Lee-Txwg/Miner_Helmet/06_FCT/Wordpress/wp-content/themes/twentytwentyfour/assets/images/tourist-and-building.webp

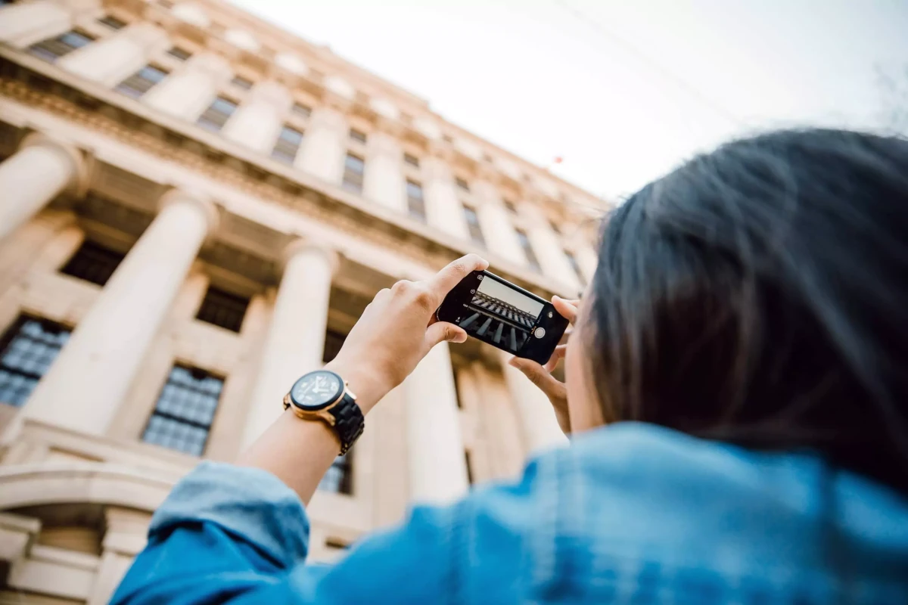
06_FCT/Wordpress/wp-content/themes/twentytwentyfour/assets/images/tourist-and-building.webp
