Lee-Txwg/Miner_Helmet/04_Software/00_Ref/【挽救小白第一季】STM32+8266+小程序智能家居毕设实战/1.使用模块硬件资料/3.esp01s网络模块/接线示例.png

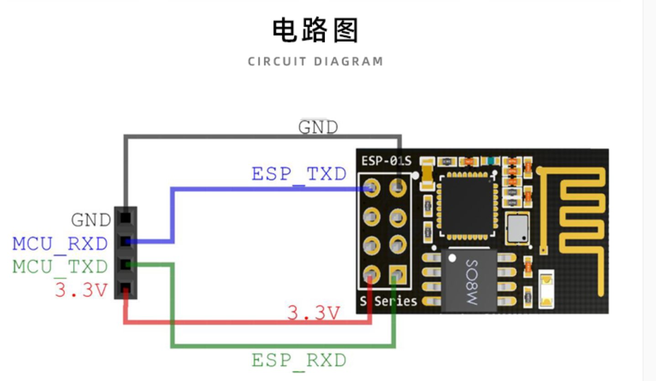
04_Software/00_Ref/【挽救小白第一季】STM32+8266+小程序智能家居毕设实战/1.使用模块硬件资料/3.esp01s网络模块/接线示例.png
