Lee-Txwg/Miner_Helmet/04_Software/00_Ref/【挽救小白第一季】STM32+8266+小程序智能家居毕设实战/1.使用模块硬件资料/4.STM32F103C8T6核心板/尺寸.jpg

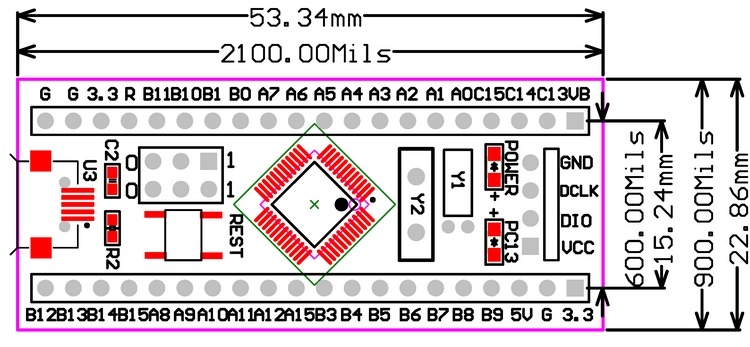
04_Software/00_Ref/【挽救小白第一季】STM32+8266+小程序智能家居毕设实战/1.使用模块硬件资料/4.STM32F103C8T6核心板/尺寸.jpg
