Lee-Txwg/Miner_Helmet/04_Software/00_Ref/【挽救小白第一季】STM32+8266+小程序智能家居毕设实战/2.扩展板硬件设计资料/v1.5(在售)/1.预览图片/2D_bottom_v1.5.png

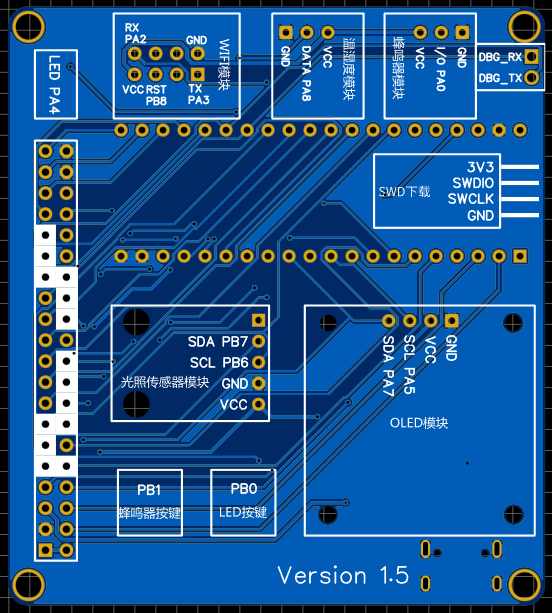
04_Software/00_Ref/【挽救小白第一季】STM32+8266+小程序智能家居毕设实战/2.扩展板硬件设计资料/v1.5(在售)/1.预览图片/2D_bottom_v1.5.png
