Lee-Txwg/Miner_Helmet/06_FCT/Wordpress/wp-admin/images/about-texture.png

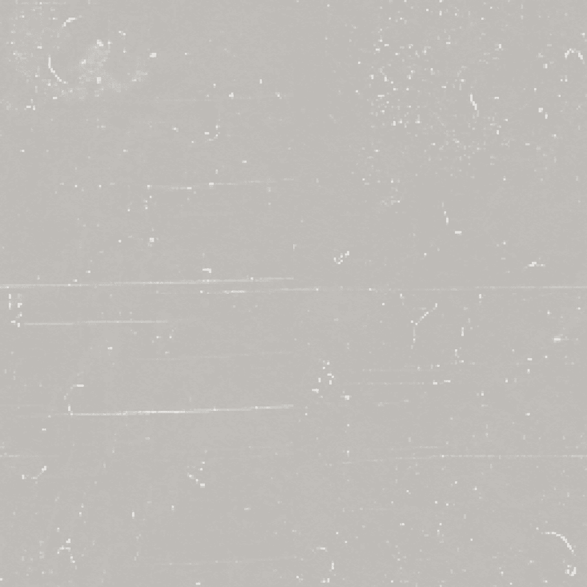
06_FCT/Wordpress/wp-admin/images/about-texture.png
