Lee-Txwg/Miner_Helmet/06_FCT/Wordpress/wp-admin/images/browser-rtl.png

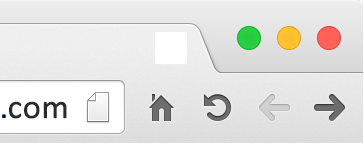
06_FCT/Wordpress/wp-admin/images/browser-rtl.png
