Lee-Txwg/Miner_Helmet/06_FCT/Wordpress/wp-admin/images/wheel.png

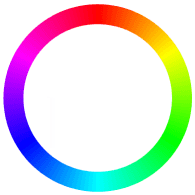
06_FCT/Wordpress/wp-admin/images/wheel.png
