Lee-Txwg/Miner_Helmet/06_FCT/Wordpress/wp-content/themes/twentytwentyfive/assets/images/404-image.webp

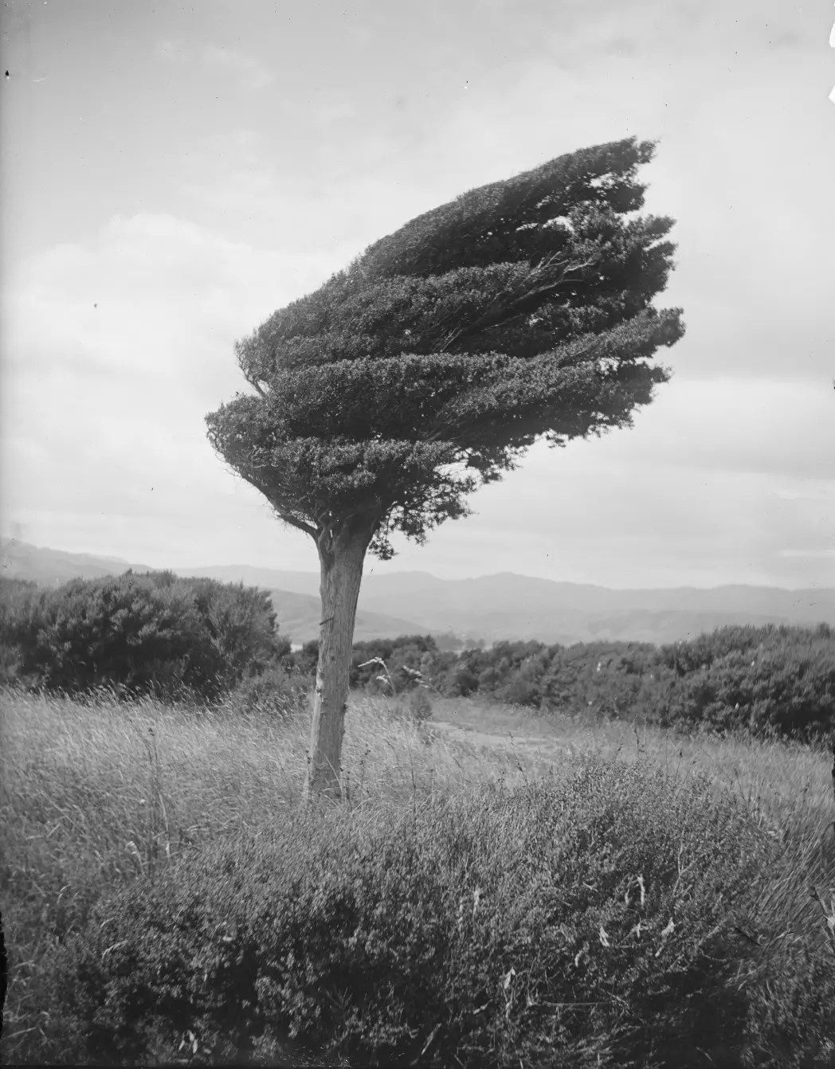
06_FCT/Wordpress/wp-content/themes/twentytwentyfive/assets/images/404-image.webp
