Lee-Txwg/Miner_Helmet/06_FCT/Wordpress/wp-content/themes/twentytwentyfive/assets/images/agenda-img-4.webp

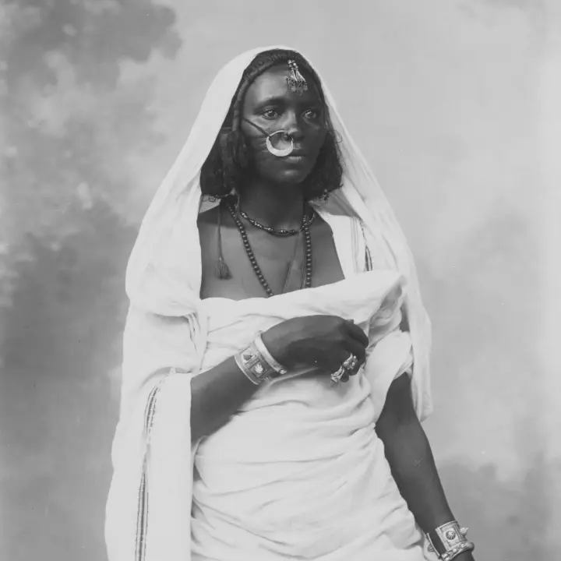
06_FCT/Wordpress/wp-content/themes/twentytwentyfive/assets/images/agenda-img-4.webp
