Lee-Txwg/Miner_Helmet/06_FCT/Wordpress/wp-content/themes/twentytwentyfive/assets/images/akaka-falls-state-park-flora.webp

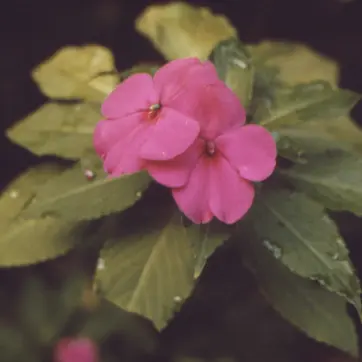
06_FCT/Wordpress/wp-content/themes/twentytwentyfive/assets/images/akaka-falls-state-park-flora.webp
