Lee-Txwg/Miner_Helmet/06_FCT/Wordpress/wp-content/themes/twentytwentyfive/assets/images/book-image-landing.webp

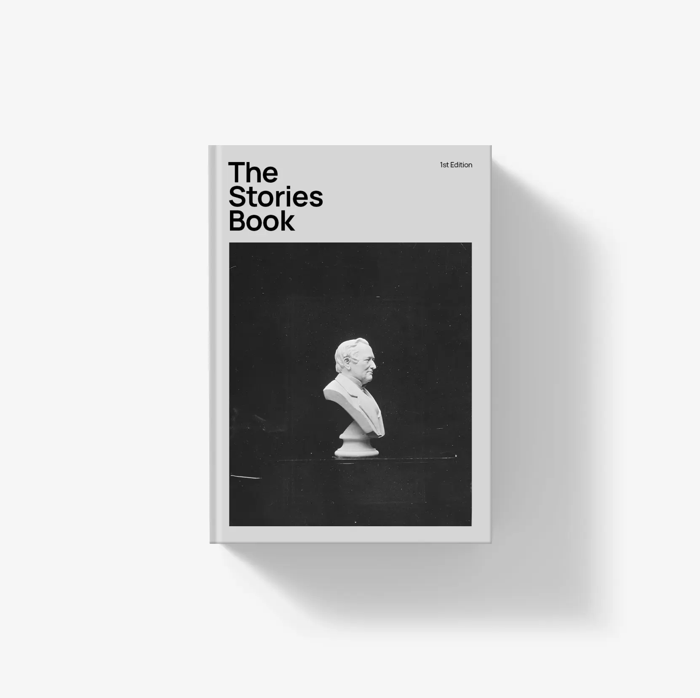
06_FCT/Wordpress/wp-content/themes/twentytwentyfive/assets/images/book-image-landing.webp
