Lee-Txwg/Miner_Helmet/06_FCT/Wordpress/wp-content/themes/twentytwentyfive/assets/images/flower-meadow-square.webp

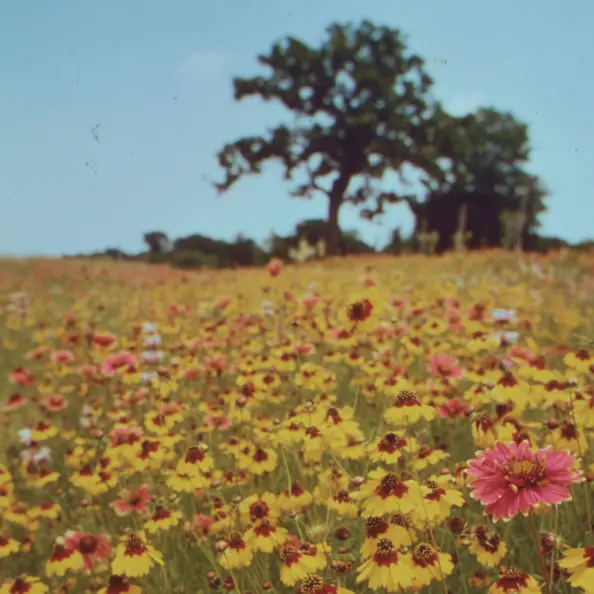
06_FCT/Wordpress/wp-content/themes/twentytwentyfive/assets/images/flower-meadow-square.webp
