Lee-Txwg/Miner_Helmet/06_FCT/Wordpress/wp-content/themes/twentytwentyfive/assets/images/grid-flower-1.webp

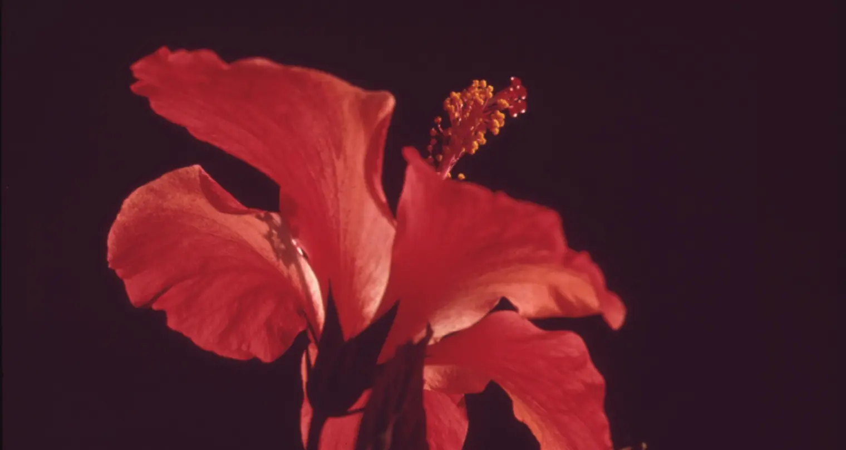
06_FCT/Wordpress/wp-content/themes/twentytwentyfive/assets/images/grid-flower-1.webp
