Lee-Txwg/Miner_Helmet/06_FCT/Wordpress/wp-content/themes/twentytwentyfive/assets/images/hero-podcast.webp

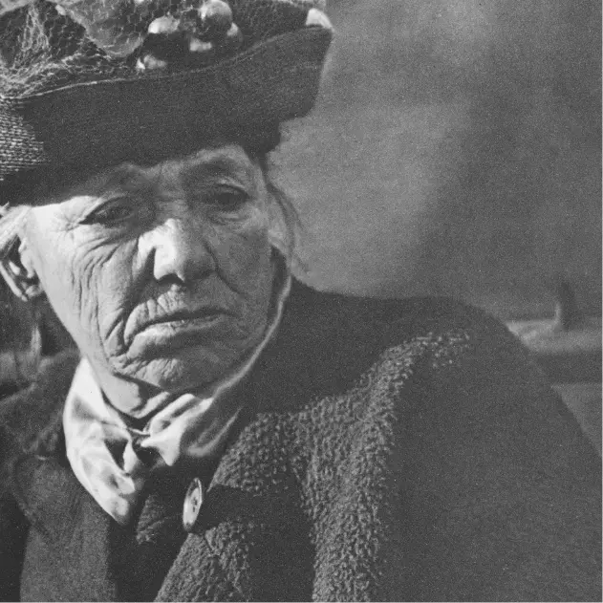
06_FCT/Wordpress/wp-content/themes/twentytwentyfive/assets/images/hero-podcast.webp
