Lee-Txwg/Miner_Helmet/06_FCT/Wordpress/wp-content/themes/twentytwentyfive/assets/images/link-in-bio-background.webp

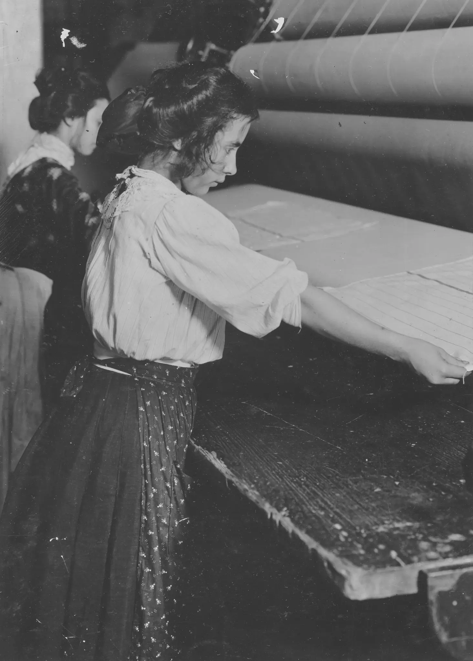
06_FCT/Wordpress/wp-content/themes/twentytwentyfive/assets/images/link-in-bio-background.webp
