Lee-Txwg/Miner_Helmet/06_FCT/Wordpress/wp-content/themes/twentytwentyfive/assets/images/man-in-hat.webp

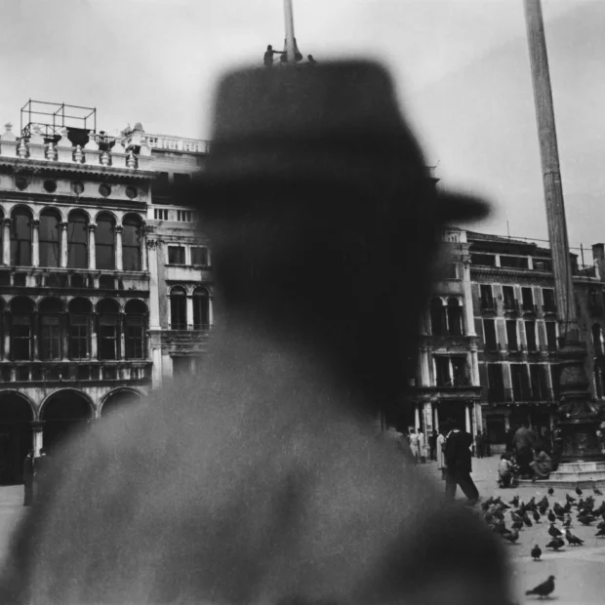
06_FCT/Wordpress/wp-content/themes/twentytwentyfive/assets/images/man-in-hat.webp
