Lee-Txwg/Miner_Helmet/06_FCT/Wordpress/wp-content/themes/twentytwentyfive/assets/images/northern-buttercups-flowers.webp

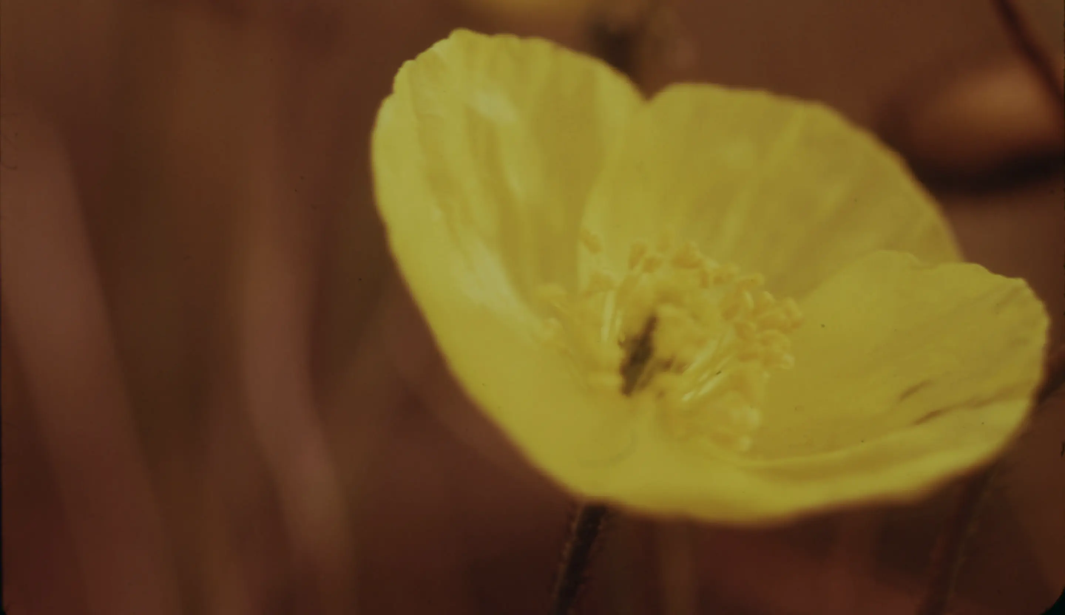
06_FCT/Wordpress/wp-content/themes/twentytwentyfive/assets/images/northern-buttercups-flowers.webp
