Lee-Txwg/Miner_Helmet/06_FCT/Wordpress/wp-content/themes/twentytwentyfive/assets/images/red-hibiscus-closeup.webp

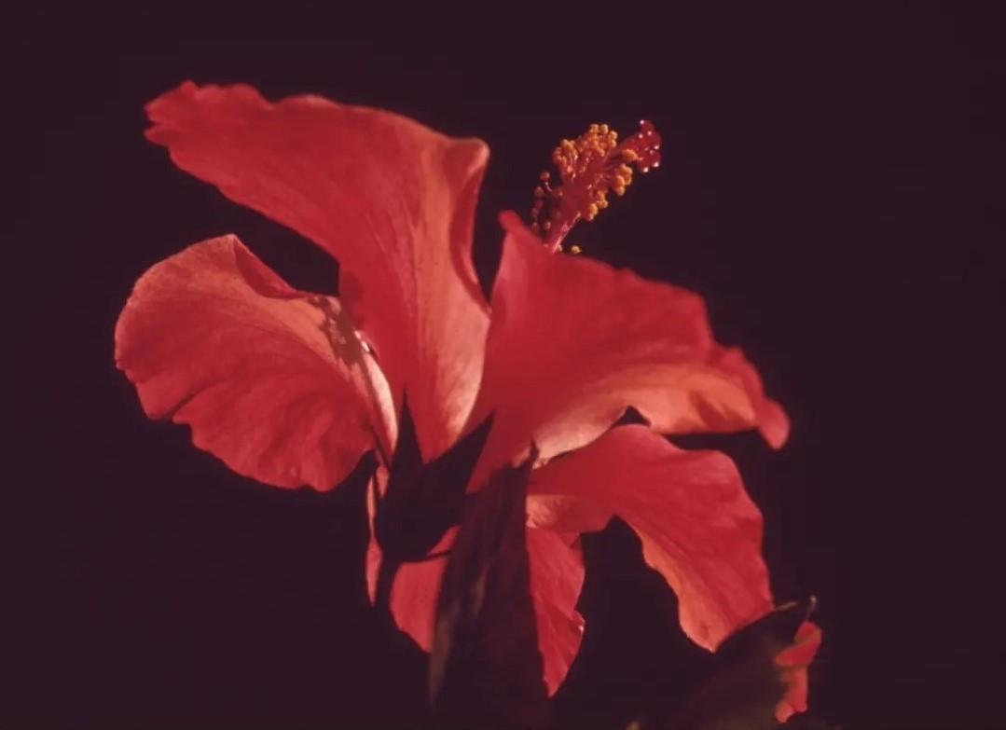
06_FCT/Wordpress/wp-content/themes/twentytwentyfive/assets/images/red-hibiscus-closeup.webp
