Lee-Txwg/Miner_Helmet/06_FCT/Wordpress/wp-content/themes/twentytwentyfive/assets/images/services-subscriber-photo.webp

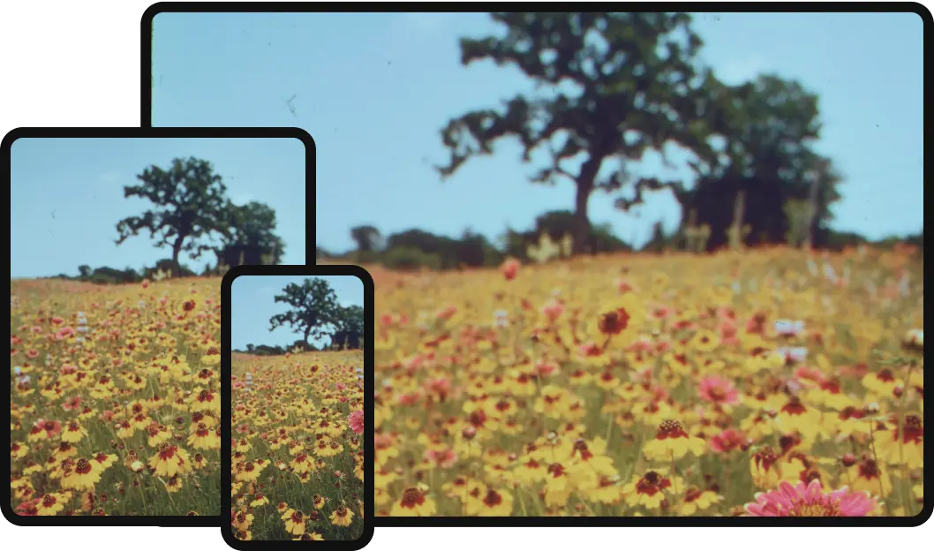
06_FCT/Wordpress/wp-content/themes/twentytwentyfive/assets/images/services-subscriber-photo.webp
