Lee-Txwg/Miner_Helmet/06_FCT/Wordpress/wp-content/themes/twentytwentyfive/assets/images/star-thristle-flower.webp

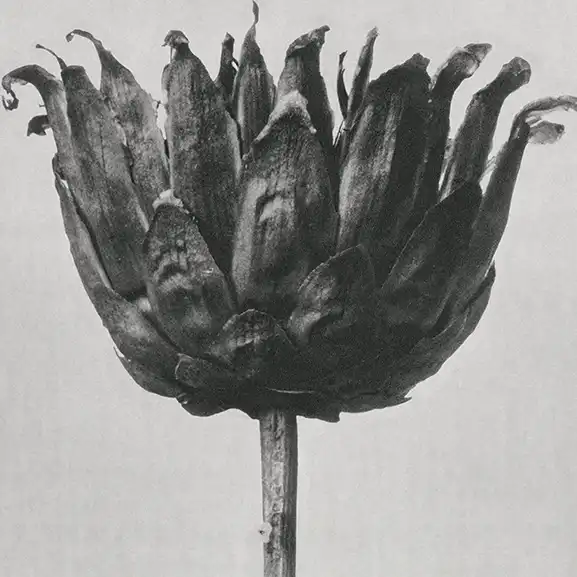
06_FCT/Wordpress/wp-content/themes/twentytwentyfive/assets/images/star-thristle-flower.webp
