Lee-Txwg/Miner_Helmet/06_FCT/Wordpress/wp-content/themes/twentytwentyfive/screenshot.png

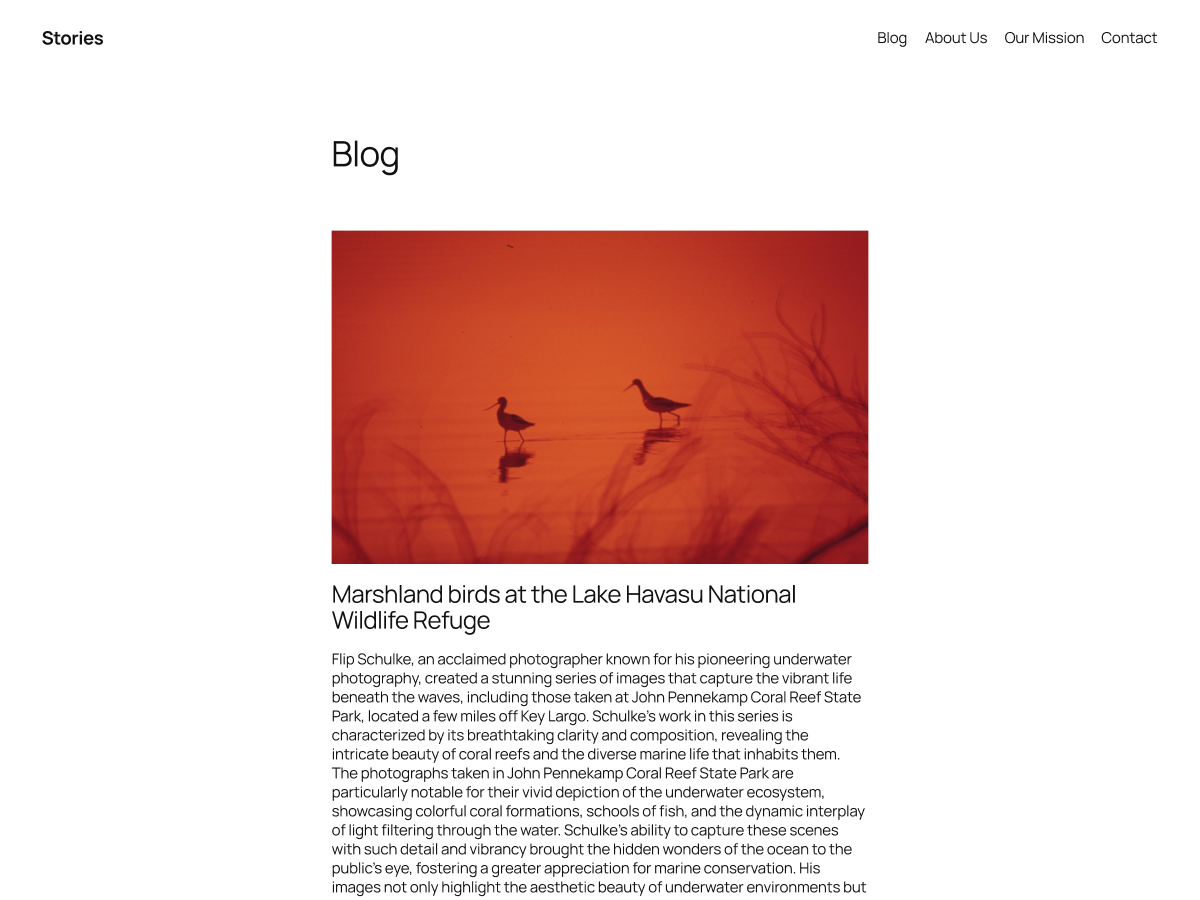
06_FCT/Wordpress/wp-content/themes/twentytwentyfive/screenshot.png
