Lee-Txwg/Miner_Helmet/06_FCT/Wordpress/wp-content/themes/twentytwentyfour/assets/images/abstract-geometric-art.webp

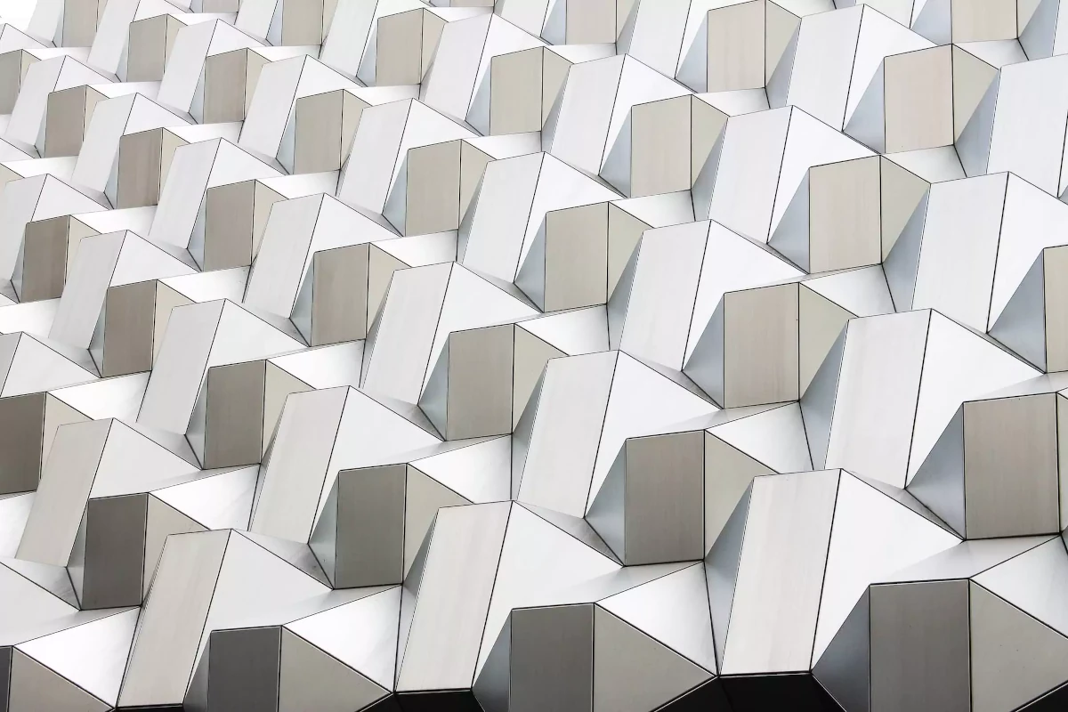
06_FCT/Wordpress/wp-content/themes/twentytwentyfour/assets/images/abstract-geometric-art.webp
