Lee-Txwg/Miner_Helmet/06_FCT/Wordpress/wp-content/themes/twentytwentyfour/assets/images/green-staircase.webp

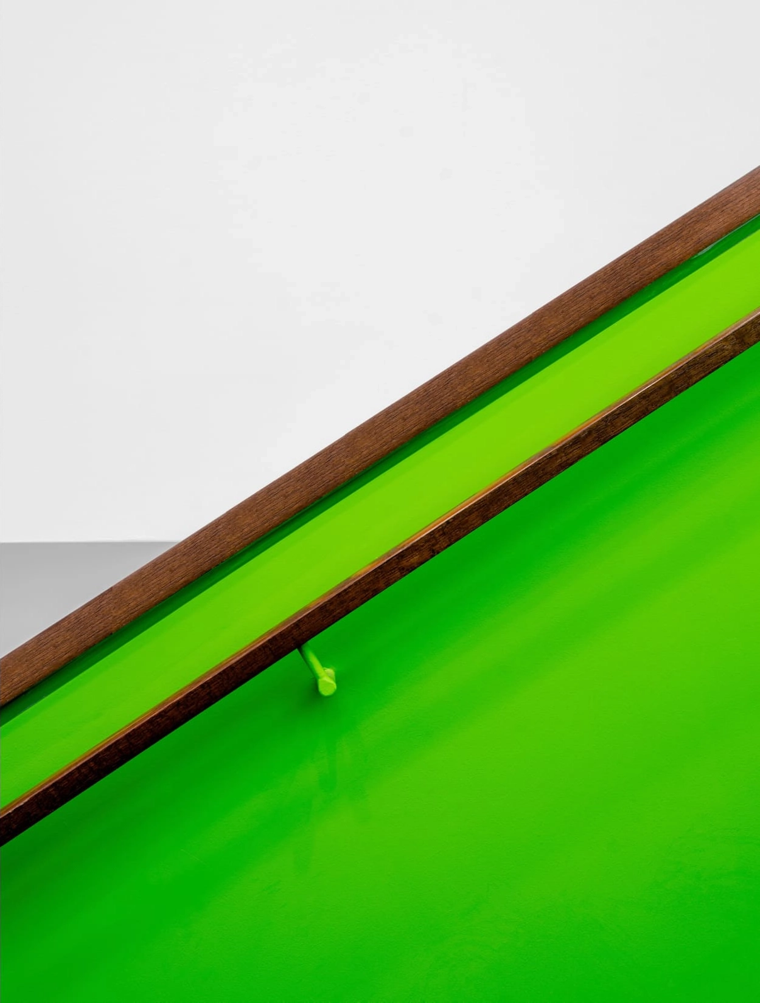
06_FCT/Wordpress/wp-content/themes/twentytwentyfour/assets/images/green-staircase.webp
