Lee-Txwg/Miner_Helmet/06_FCT/Wordpress/wp-content/themes/twentytwentyfour/assets/images/hotel-facade.webp

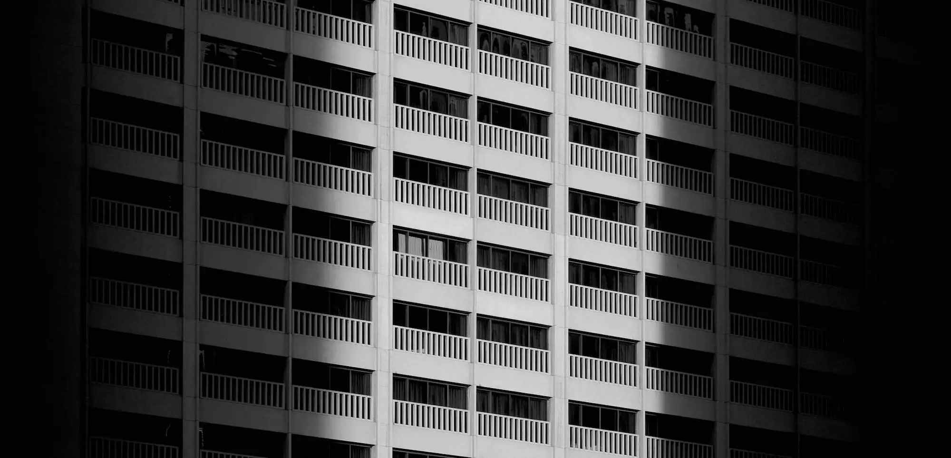
06_FCT/Wordpress/wp-content/themes/twentytwentyfour/assets/images/hotel-facade.webp
