Lee-Txwg/Miner_Helmet/06_FCT/Wordpress/wp-content/themes/twentytwentyfour/assets/images/museum.webp

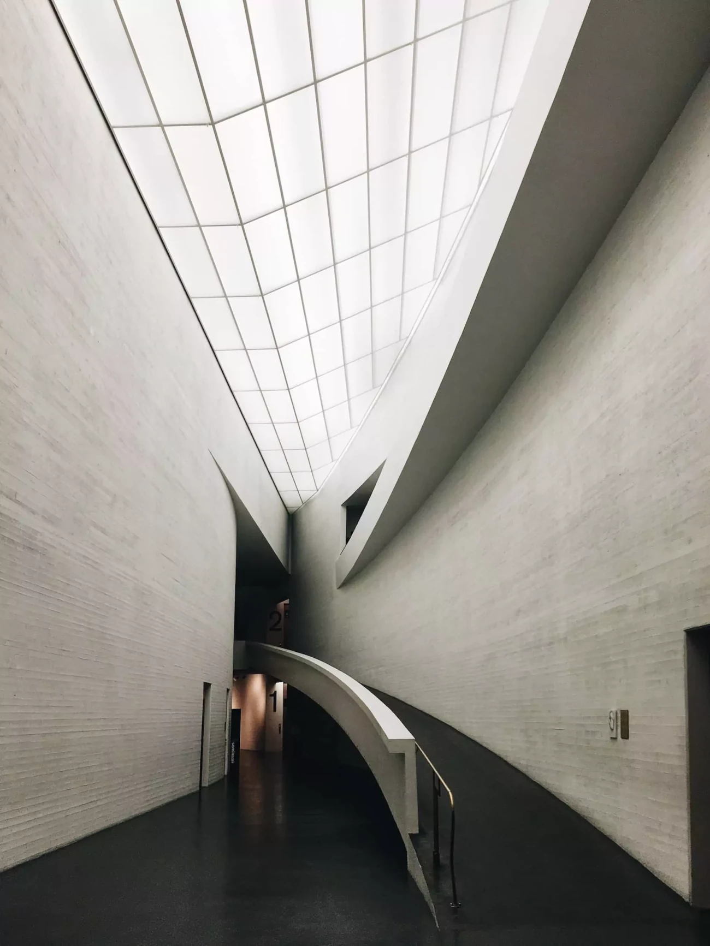
06_FCT/Wordpress/wp-content/themes/twentytwentyfour/assets/images/museum.webp
