Lee-Txwg/Miner_Helmet/06_FCT/Wordpress/wp-content/themes/twentytwentythree/screenshot.png

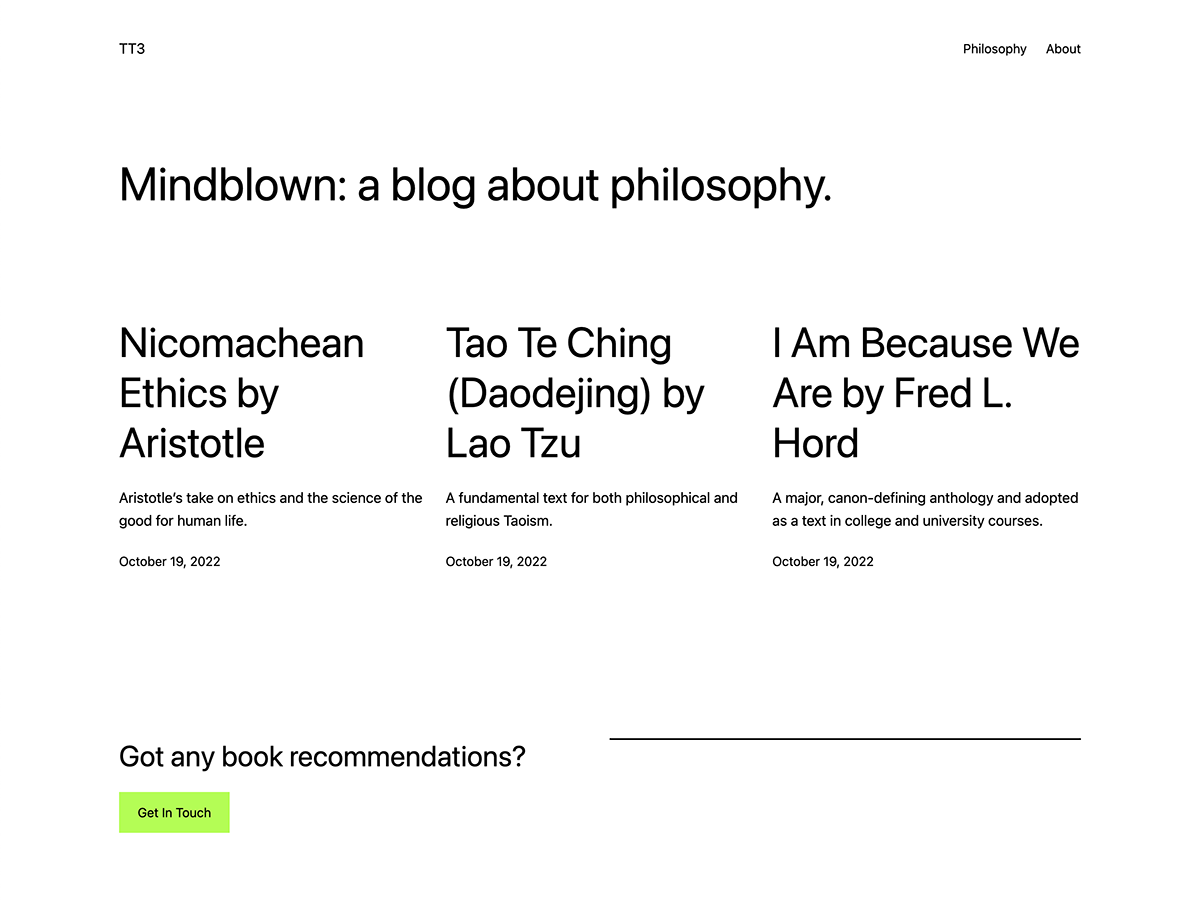
06_FCT/Wordpress/wp-content/themes/twentytwentythree/screenshot.png
