Lee-Txwg/Miner_Helmet/06_FCT/Wordpress/wp-content/themes/twentytwentytwo/assets/images/bird-on-black.jpg

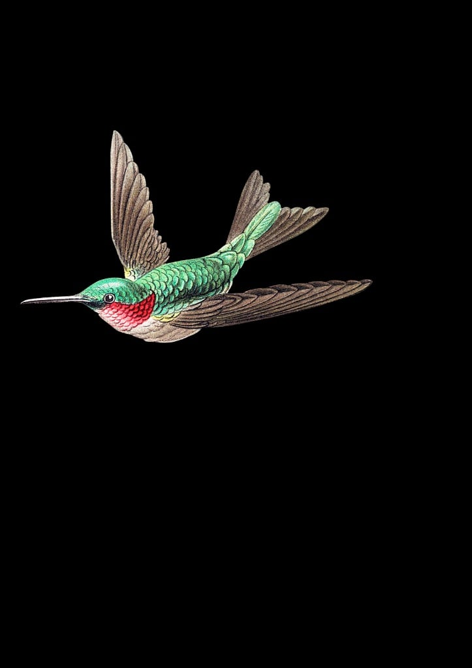
06_FCT/Wordpress/wp-content/themes/twentytwentytwo/assets/images/bird-on-black.jpg
