Lee-Txwg/Miner_Helmet/06_FCT/Wordpress/wp-content/themes/twentytwentytwo/assets/images/divider-black.png

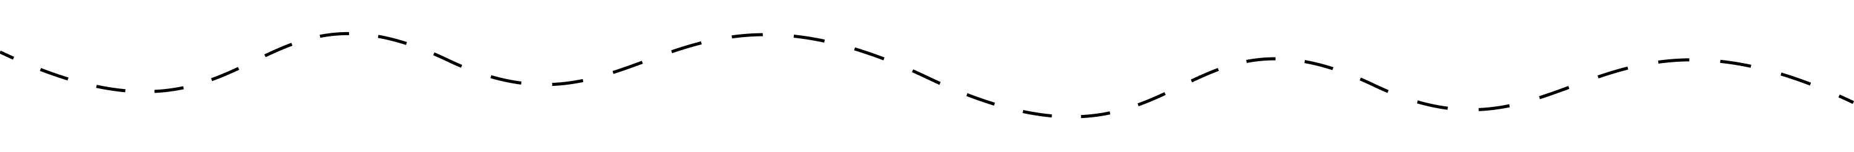
06_FCT/Wordpress/wp-content/themes/twentytwentytwo/assets/images/divider-black.png
