Lee-Txwg/Miner_Helmet/06_FCT/Wordpress/wp-content/themes/twentytwentytwo/assets/images/divider-white.png

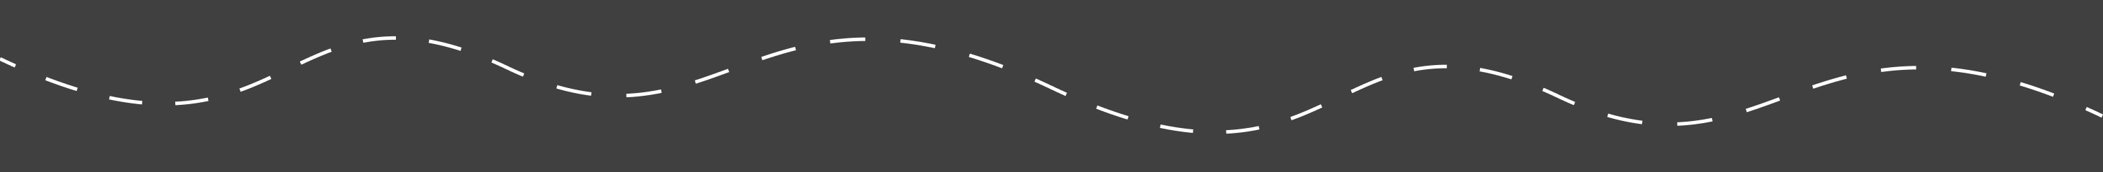
06_FCT/Wordpress/wp-content/themes/twentytwentytwo/assets/images/divider-white.png
