Lee-Txwg/Miner_Helmet/06_FCT/Wordpress/wp-content/themes/twentytwentytwo/assets/images/ducks.jpg

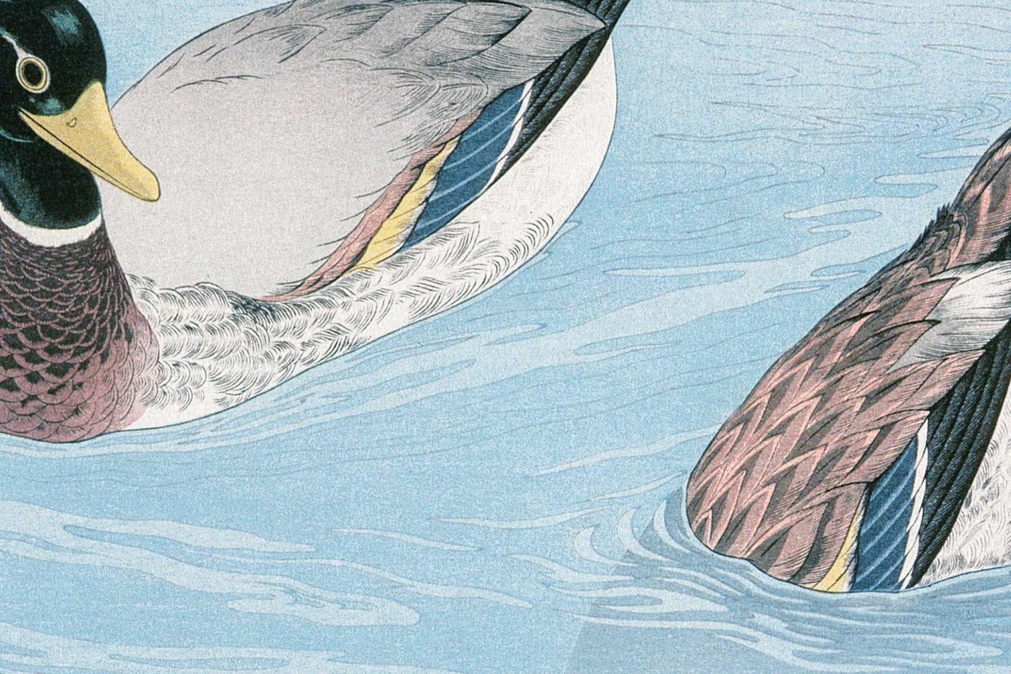
06_FCT/Wordpress/wp-content/themes/twentytwentytwo/assets/images/ducks.jpg
