Lee-Txwg/Miner_Helmet/06_FCT/Wordpress/wp-content/themes/twentytwentytwo/assets/images/flight-path-on-salmon.jpg

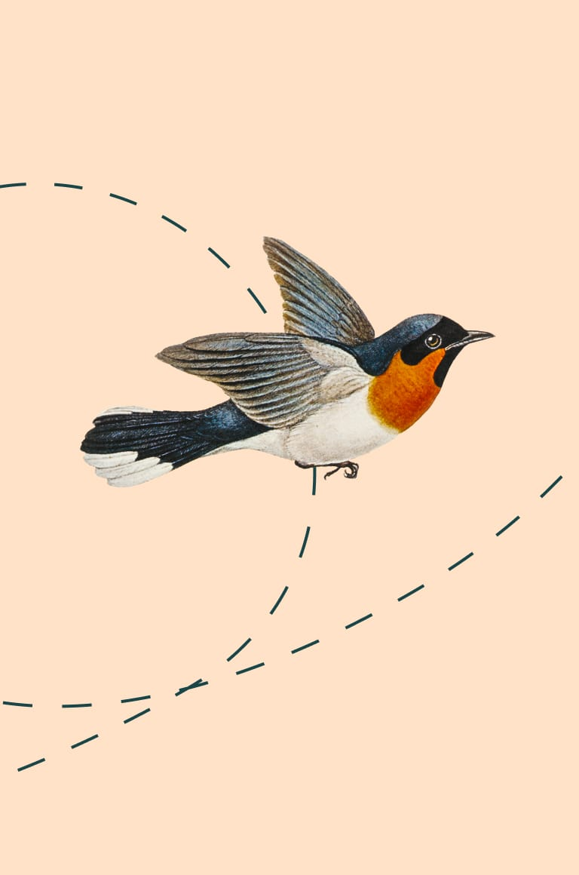
06_FCT/Wordpress/wp-content/themes/twentytwentytwo/assets/images/flight-path-on-salmon.jpg
