Lee-Txwg/Miner_Helmet/06_FCT/Wordpress/wp-content/themes/twentytwentytwo/screenshot.png

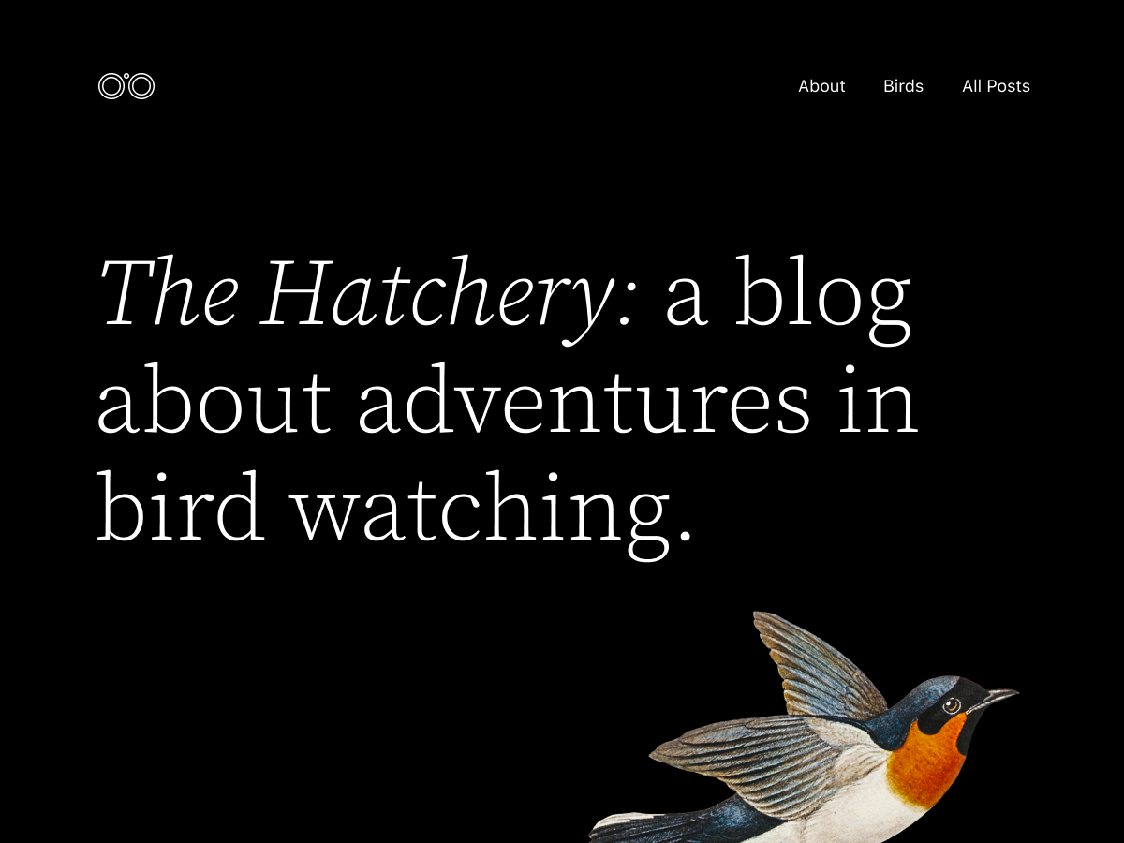
06_FCT/Wordpress/wp-content/themes/twentytwentytwo/screenshot.png
