Lee-Txwg/Miner_Helmet/06_FCT/Wordpress/wp-includes/js/mediaelement/mejs-controls.png

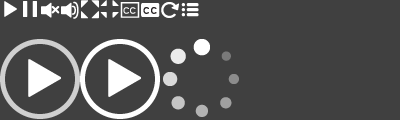
06_FCT/Wordpress/wp-includes/js/mediaelement/mejs-controls.png
