Lee-Txwg/Miner_Helmet/02_Hardware/01_Project/01_AD/MineSafe-circular-board/material/Doc1.docx

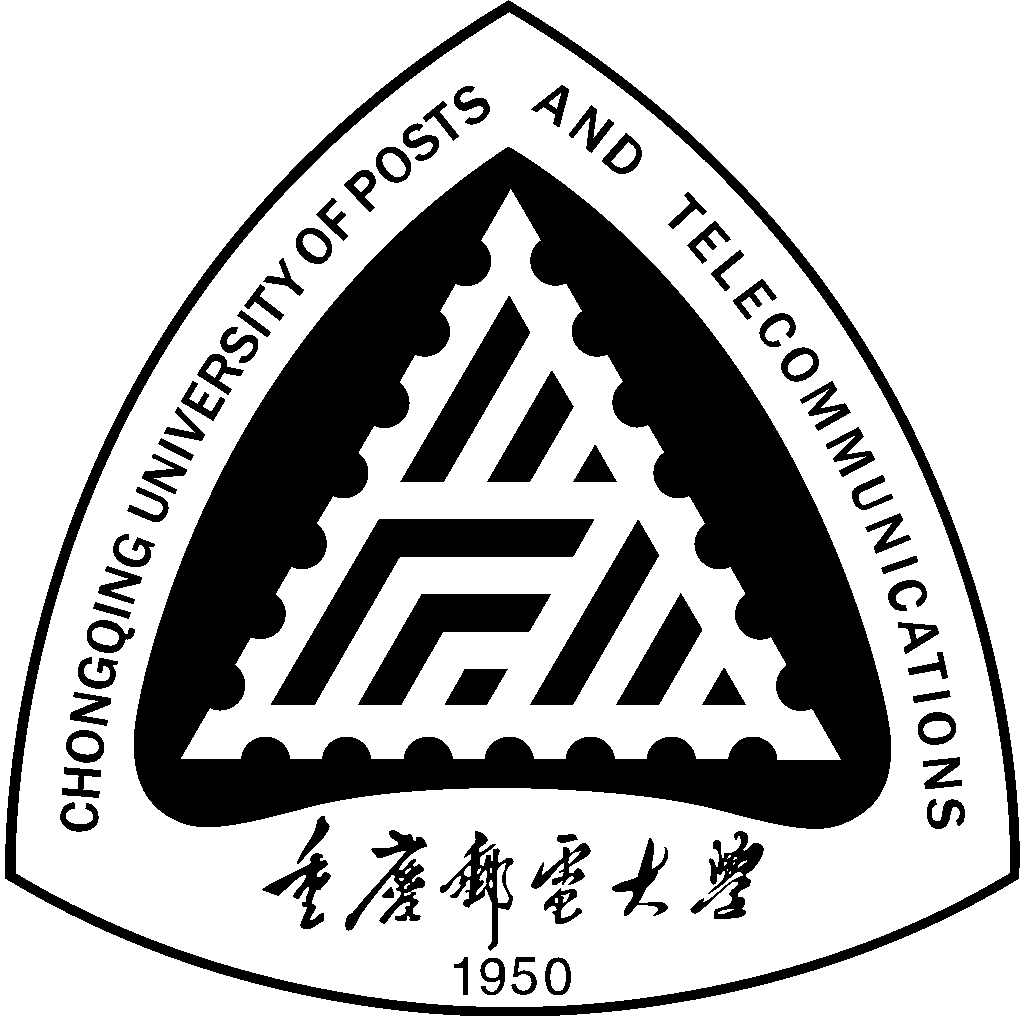
[picture p110: figure]
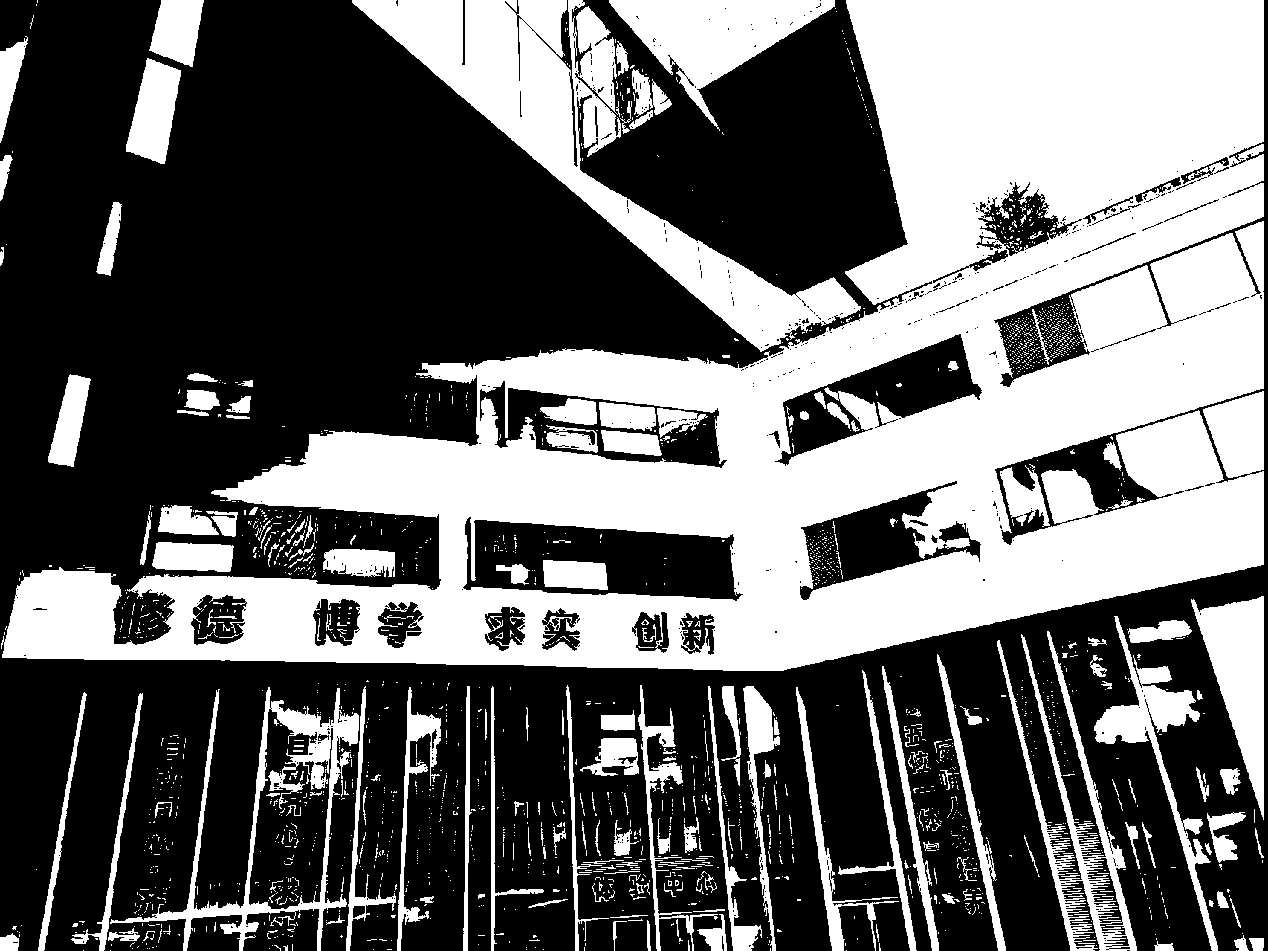
[picture p111: figure]
