Lee-Txwg/Miner_Helmet/02_Hardware/01_Project/01_AD/MineSafe-circular-board/material/github.png

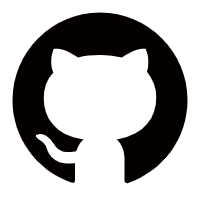
02_Hardware/01_Project/01_AD/MineSafe-circular-board/material/github.png
