Lee-Txwg/Miner_Helmet/02_Hardware/01_Project/01_AD/MineSafe-rectangle-board/material/微信图片_20250417230446.jpg

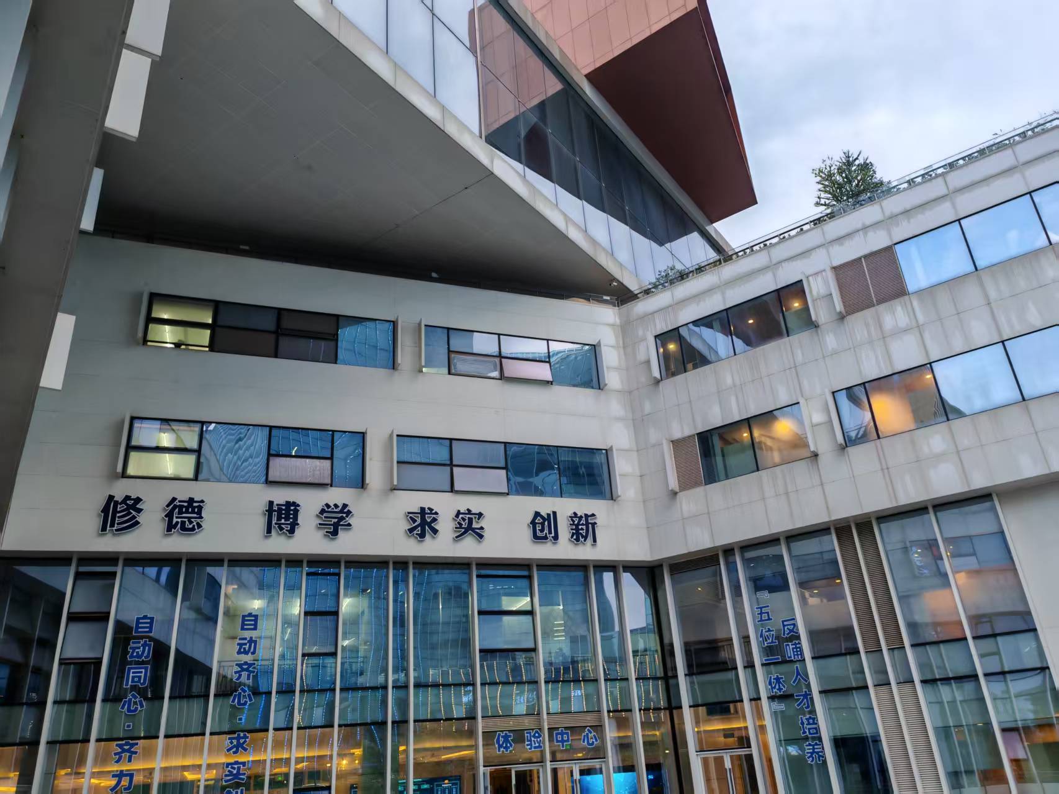
02_Hardware/01_Project/01_AD/MineSafe-rectangle-board/material/微信图片_20250417230446.jpg
