Lee-Txwg/Miner_Helmet/04_Software/00_Ref/ESP8266/03_c8t6/MDK-ARM/pid.c

/* Includes ------------------------------------------------------------------*/
 #include "pid.h"
#include "mytype.h"
#include <math.h>
//#include "cmsis_os.h"

#define ABS(x)		((x>0)? (x): (-x)) 

void abs_limit(float *a, float ABS_MAX){
    if(*a > ABS_MAX)
        *a = ABS_MAX;
    if(*a < -ABS_MAX)
        *a = -ABS_MAX;
}
/*参数初始化--------------------------------------------------------------*/
static void pid_param_init(
    pid_t *pid, 
    uint32_t mode,
    uint32_t maxout,
    uint32_t intergral_limit,
    float 	kp, 
    float 	ki, 
    float 	kd)
{
    
    pid->IntegralLimit = intergral_limit;
    pid->MaxOutput = maxout;
    pid->pid_mode = mode;
    
    pid->p = kp;
    pid->i = ki;
    pid->d = kd;
    
}
/*中途更改参数设定(调试)------------------------------------------------------------*/
static void pid_reset(pid_t	*pid, float kp, float ki, float kd)
{
    pid->p = kp;
    pid->i = ki;
    pid->d = kd;
}


float pid_calc(pid_t* pid, float get, float set,int type){
    pid->get[NOW] = get;
    pid->set[NOW] = set;
    pid->err[NOW] = set - get;	//set - measure
	if(type==1)
{
	  if(pid->err[NOW]>4095)
			pid->err[NOW]-=8192;
		else if(pid->err[NOW]<-4095)
			pid->err[NOW]+=8192;
}
    if (pid->max_err != 0 && ABS(pid->err[NOW]) >  pid->max_err  )
		return 0;
	if (pid->deadband != 0 && ABS(pid->err[NOW]) < pid->deadband)
		return 0;
    
    if(pid->pid_mode == POSITION_PID) //位置式p
    {
        pid->pout = pid->p * pid->err[NOW];
        pid->iout += pid->i * pid->err[NOW];
        pid->dout = pid->d * (pid->err[NOW] - pid->err[LAST] );
        abs_limit(&(pid->iout), pid->IntegralLimit);
        pid->pos_out = pid->pout + pid->iout + pid->dout;
        abs_limit(&(pid->pos_out), pid->MaxOutput);
        pid->last_pos_out = pid->pos_out;	//update last time 
    }
    else if(pid->pid_mode == DELTA_PID)//增量式P
    {
        pid->pout = pid->p * (pid->err[NOW] - pid->err[LAST]);
        pid->iout = pid->i * pid->err[NOW];
        pid->dout = pid->d * (pid->err[NOW] - 2*pid->err[LAST] + pid->err[LLAST]);
        
        abs_limit(&(pid->iout), pid->IntegralLimit);
        pid->delta_u = pid->pout + pid->iout + pid->dout;
        pid->delta_out = pid->last_delta_out + pid->delta_u;
        abs_limit(&(pid->delta_out), pid->MaxOutput);
        pid->last_delta_out = pid->delta_out;	//update last time
    }
    
    pid->err[LLAST] = pid->err[LAST];
    pid->err[LAST] = pid->err[NOW];
    pid->get[LLAST] = pid->get[LAST];
    pid->get[LAST] = pid->get[NOW];
    pid->set[LLAST] = pid->set[LAST];
    pid->set[LAST] = pid->set[NOW];
    return pid->pid_mode==POSITION_PID ? pid->pos_out : pid->delta_out;
	
}





/*pid总体初始化-----------------------------------------------------------------*/
void PID_struct_init(
    pid_t* pid,
    uint32_t mode,
    uint32_t maxout,
    uint32_t intergral_limit,
    
    float 	kp, 
    float 	ki, 
    float 	kd)
{
    
    pid->f_param_init = pid_param_init;
    pid->f_pid_reset = pid_reset;

    pid->f_param_init(pid, mode, maxout, intergral_limit, kp, ki, kd);
	
}


void PID_set(
    pid_t* pid,
    float 	kp, 
    float 	ki, 
    float 	kd)
{
    
  
    pid->f_pid_reset = pid_reset;

    pid->f_pid_reset(pid, kp, ki, kd);
	
}





pid_t pid_spd[4];
pid_t pid_spd1[4];
pid_t pid_spd2[4];
