Lee-Txwg/Miner_Helmet/04_Software/02_stable/HARDWARE/GPS/gps.c

#include "gps.h"  
#include "sys.h"
#include "string.h"	
#include "oled.h"
#include "delay.h"
#include "stdio.h"
#include "usart.h"


__align(8) uint8_t USART3_TX_BUF[USART_MAX_SEND_LEN];
uint8_t USART3_RX_BUF[USART_MAX_RECV_LEN];



static void Com_SendData(uint8_t data)
{
	
	USART_SendData(USART3, data);
	while(USART_GetFlagStatus(USART3, USART_FLAG_TXE) == RESET);

}

void HAL_UART_Transmit(USART_TypeDef* USARTx,  uint8_t *pData, uint16_t Size)
{
	uint16_t i;
	for(i=0;i<Size;i++)
	{
	Com_SendData(*(pData+i));
	}
}
uint8_t NMEA_Comma_Pos(uint8_t *buf,uint8_t cx)
{	 		    
	uint8_t *p=buf;
	while(cx)
	{		 
		if(*buf=='*'||*buf<' '||*buf>'z')return 0XFF;
		if(*buf==',')cx--;
		buf++;
	}
	return buf-p;	 
}


uint32_t NMEA_Pow(uint8_t m,uint8_t n)
{
	uint32_t result=1;	 
	while(n--)result*=m;    
	return result;
}




int NMEA_Str2num(uint8_t *buf,uint8_t*dx)
{
	uint8_t *p=buf;
	uint32_t ires=0,fres=0;
	uint8_t ilen=0,flen=0,i;
	uint8_t mask=0;
	int res;
	while(1)
	{
		if(*p=='-'){mask|=0X02;p++;}
		if(*p==','||(*p=='*'))break;
		if(*p=='.'){mask|=0X01;p++;}
		else if(*p>'9'||(*p<'0'))
		{	
			ilen=0;
			flen=0;
			break;
		}	
		if(mask&0X01)flen++;
		else ilen++;
		p++;
	}
	if(mask&0X02)buf++;
	for(i=0;i<ilen;i++)
	{  
		ires+=NMEA_Pow(10,ilen-1-i)*(buf[i]-'0');
	}
	if(flen>5)flen=5;
	*dx=flen;
	for(i=0;i<flen;i++)
	{  
		fres+=NMEA_Pow(10,flen-1-i)*(buf[ilen+1+i]-'0');
	} 
	res=ires*NMEA_Pow(10,flen)+fres;
	if(mask&0X02)res=-res;		   
	return res;
}	  							 



void NMEA_GPGSV_Analysis(nmea_msg *gpsx,uint8_t *buf)
{
	uint8_t *p,*p1,dx;
	uint8_t len,i,j,slx=0;
	uint8_t posx;   	 
	p=buf;
	p1=(uint8_t*)strstr((const char *)p,"$GPGSV");
	len=p1[7]-'0';
	posx=NMEA_Comma_Pos(p1,3);
	if(posx!=0XFF)gpsx->svnum=NMEA_Str2num(p1+posx,&dx);
	for(i=0;i<len;i++)
	{	 
		p1=(uint8_t*)strstr((const char *)p,"$GPGSV");  
		for(j=0;j<4;j++)
		{	  
			posx=NMEA_Comma_Pos(p1,4+j*4);
			if(posx!=0XFF)gpsx->slmsg[slx].num=NMEA_Str2num(p1+posx,&dx);
			else break; 
			posx=NMEA_Comma_Pos(p1,5+j*4);
			if(posx!=0XFF)gpsx->slmsg[slx].eledeg=NMEA_Str2num(p1+posx,&dx);
			else break;
			posx=NMEA_Comma_Pos(p1,6+j*4);
			if(posx!=0XFF)gpsx->slmsg[slx].azideg=NMEA_Str2num(p1+posx,&dx);
			else break; 
			posx=NMEA_Comma_Pos(p1,7+j*4);
			if(posx!=0XFF)gpsx->slmsg[slx].sn=NMEA_Str2num(p1+posx,&dx);
			else break;
			slx++;	   
		}   
 		p=p1+1;
	}   
}



void NMEA_GPGGA_Analysis(nmea_msg *gpsx,uint8_t *buf)
{
	uint8_t *p1,dx;			 
	uint8_t posx;    
	p1=(uint8_t*)strstr((const char *)buf,"$GPGGA");
	posx=NMEA_Comma_Pos(p1,6);
	if(posx!=0XFF)gpsx->gpssta=NMEA_Str2num(p1+posx,&dx);	
	posx=NMEA_Comma_Pos(p1,7);
	if(posx!=0XFF)gpsx->posslnum=NMEA_Str2num(p1+posx,&dx); 
	posx=NMEA_Comma_Pos(p1,9);
	if(posx!=0XFF)gpsx->altitude=NMEA_Str2num(p1+posx,&dx);  
}



void NMEA_GPGSA_Analysis(nmea_msg *gpsx,uint8_t *buf)
{
	uint8_t *p1,dx;			 
	uint8_t posx; 
	uint8_t i;   
	p1=(uint8_t*)strstr((const char *)buf,"$GPGSA");
	posx=NMEA_Comma_Pos(p1,2);
	if(posx!=0XFF)gpsx->fixmode=NMEA_Str2num(p1+posx,&dx);	
	for(i=0;i<12;i++)
	{
		posx=NMEA_Comma_Pos(p1,3+i);					 
		if(posx!=0XFF)gpsx->possl[i]=NMEA_Str2num(p1+posx,&dx);
		else break; 
	}				  
	posx=NMEA_Comma_Pos(p1,15);
	if(posx!=0XFF)gpsx->pdop=NMEA_Str2num(p1+posx,&dx);  
	posx=NMEA_Comma_Pos(p1,16);
	if(posx!=0XFF)gpsx->hdop=NMEA_Str2num(p1+posx,&dx);  
	posx=NMEA_Comma_Pos(p1,17);
	if(posx!=0XFF)gpsx->vdop=NMEA_Str2num(p1+posx,&dx);  
}



void NMEA_GPRMC_Analysis(nmea_msg *gpsx,uint8_t *buf)
{
	uint8_t *p1,dx;			 
	uint8_t posx;     
	uint32_t temp;	   
	float rs;  
	p1=(uint8_t*)strstr((const char *)buf,"GPRMC");
	posx=NMEA_Comma_Pos(p1,1);
	if(posx!=0XFF)
	{
		temp=NMEA_Str2num(p1+posx,&dx)/NMEA_Pow(10,dx);
		gpsx->utc.hour=temp/10000;
		gpsx->utc.min=(temp/100)%100;
		gpsx->utc.sec=temp%100;	 	 
	}	
	posx=NMEA_Comma_Pos(p1,3);
	if(posx!=0XFF)
	{
		temp=NMEA_Str2num(p1+posx,&dx);		 	 
		gpsx->latitude=temp/NMEA_Pow(10,dx+2);
		rs=temp%NMEA_Pow(10,dx+2);
		gpsx->latitude=gpsx->latitude*NMEA_Pow(10,5)+(rs*NMEA_Pow(10,5-dx))/60;
	}
	posx=NMEA_Comma_Pos(p1,4);
	if(posx!=0XFF)gpsx->nshemi=*(p1+posx);					 
 	posx=NMEA_Comma_Pos(p1,5);
	if(posx!=0XFF)
	{												  
		temp=NMEA_Str2num(p1+posx,&dx);		 	 
		gpsx->longitude=temp/NMEA_Pow(10,dx+2);
		rs=temp%NMEA_Pow(10,dx+2);
		gpsx->longitude=gpsx->longitude*NMEA_Pow(10,5)+(rs*NMEA_Pow(10,5-dx))/60;
	}
	posx=NMEA_Comma_Pos(p1,6);
	if(posx!=0XFF)gpsx->ewhemi=*(p1+posx);		 
	posx=NMEA_Comma_Pos(p1,9);
	if(posx!=0XFF)
	{
		temp=NMEA_Str2num(p1+posx,&dx);
		gpsx->utc.date=temp/10000;
		gpsx->utc.month=(temp/100)%100;
		gpsx->utc.year=2000+temp%100;	 	 
	} 
}



void NMEA_GPVTG_Analysis(nmea_msg *gpsx,uint8_t *buf)
{
	uint8_t *p1,dx;			 
	uint8_t posx;    
	p1=(uint8_t*)strstr((const char *)buf,"$GPVTG");							 
	posx=NMEA_Comma_Pos(p1,7);
	if(posx!=0XFF)
	{
		gpsx->speed=NMEA_Str2num(p1+posx,&dx);
		if(dx<3)gpsx->speed*=NMEA_Pow(10,3-dx);
	}
}  



void GPS_Analysis(nmea_msg *gpsx,uint8_t *buf)
{
	NMEA_GPGSV_Analysis(gpsx,buf);
	NMEA_GPGGA_Analysis(gpsx,buf);
	NMEA_GPGSA_Analysis(gpsx,buf);
	NMEA_GPRMC_Analysis(gpsx,buf);
	NMEA_GPVTG_Analysis(gpsx,buf);
}





void Ublox_CheckSum(uint8_t *buf,uint16_t len,uint8_t* cka,uint8_t*ckb)
{
	uint16_t i;
	*cka=0;*ckb=0;
	for(i=0;i<len;i++)
	{
		*cka=*cka+buf[i];
		*ckb=*ckb+*cka;
	}
}
extern uint16_t RX_len;







uint8_t Ublox_Cfg_Ack_Check(void)
{			 
	uint16_t len=0,i;
	uint8_t rval=0;
	while(RX_len==0 && len<100)
	{
		len++;
		delay_ms(5);
	}		 
	if(RX_len)
	{
		len=RX_len;
		for(i=0;i<len;i++)if(USART3_RX_BUF[i]==0XB5)break;
		if(i==len)rval=2;
		else if(USART3_RX_BUF[i+3]==0X00)rval=3;
		else rval=0;
	}else rval=1;
	return rval;  
}



uint8_t Ublox_Cfg_Cfg_Save(void)
{
	uint8_t i;
	_ublox_cfg_cfg *cfg_cfg=(_ublox_cfg_cfg *)USART3_TX_BUF;
	cfg_cfg->header=0X62B5;		//cfg header
	cfg_cfg->id=0X0906;			//cfg cfg id
	cfg_cfg->dlength=13;
	cfg_cfg->clearmask=0;
	cfg_cfg->savemask=0XFFFF;
	cfg_cfg->loadmask=0;
	cfg_cfg->devicemask=4;
	Ublox_CheckSum((uint8_t*)(&cfg_cfg->id),sizeof(_ublox_cfg_cfg)-4,&cfg_cfg->cka,&cfg_cfg->ckb);	
	HAL_UART_Transmit(USART3, (uint8_t *)&USART3_TX_BUF, sizeof(_ublox_cfg_cfg));
	
	for(i=0;i<6;i++)if(Ublox_Cfg_Ack_Check()==0)break;
	return i==6?1:0;
}


//      00,GPGGA;01,GPGLL;02,GPGSA;
//		03,GPGSV;04,GPRMC;05,GPVTG;
//		06,GPGRS;07,GPGST;08,GPZDA;
//		09,GPGBS;0A,GPDTM;0D,GPGNS;


uint8_t Ublox_Cfg_Msg(uint8_t msgid,uint8_t uart1set)
{
	_ublox_cfg_msg *cfg_msg=(_ublox_cfg_msg *)USART3_TX_BUF;
	cfg_msg->header=0X62B5;		//cfg header
	cfg_msg->id=0X0106;			//cfg msg id
	cfg_msg->dlength=8;
	cfg_msg->msgclass=0XF0;
	cfg_msg->msgid=msgid;
	cfg_msg->iicset=1;
	cfg_msg->uart1set=uart1set;
	cfg_msg->uart2set=1;
	cfg_msg->usbset=1;
	cfg_msg->spiset=1;
	cfg_msg->ncset=1;
	Ublox_CheckSum((uint8_t*)(&cfg_msg->id),sizeof(_ublox_cfg_msg)-4,&cfg_msg->cka,&cfg_msg->ckb);
	HAL_UART_Transmit(USART3, (uint8_t *)&USART3_TX_BUF, sizeof(_ublox_cfg_msg));
	
	return Ublox_Cfg_Ack_Check();
}



uint8_t Ublox_Cfg_Prt(uint32_t baudrate)
{
	_ublox_cfg_prt *cfg_prt=(_ublox_cfg_prt *)USART3_TX_BUF;
	cfg_prt->header=0X62B5;		//cfg header
	cfg_prt->id=0X0006;			//cfg prt id
	cfg_prt->dlength=20;
	cfg_prt->portid=1;
	cfg_prt->reserved=0;
	cfg_prt->txready=0;
	cfg_prt->mode=0X08D0;
	cfg_prt->baudrate=baudrate;
	cfg_prt->inprotomask=0X0007;//0+1+2
	cfg_prt->outprotomask=0X0007;//0+1+2
 	cfg_prt->reserved4=0;
 	cfg_prt->reserved5=0;
	Ublox_CheckSum((uint8_t*)(&cfg_prt->id),sizeof(_ublox_cfg_prt)-4,&cfg_prt->cka,&cfg_prt->ckb);
	HAL_UART_Transmit(USART3, (uint8_t *)&USART3_TX_BUF, sizeof(_ublox_cfg_prt));
	delay_ms(200);
	USART_BaudRate_Init(baudrate);
	return Ublox_Cfg_Ack_Check();
} 





uint8_t Ublox_Cfg_Tp(uint32_t interval,uint32_t length,signed char status)
{
	_ublox_cfg_tp *cfg_tp=(_ublox_cfg_tp *)USART3_TX_BUF;
	cfg_tp->header=0X62B5;		//cfg header
	cfg_tp->id=0X0706;			//cfg tp id
	cfg_tp->dlength=20;
	cfg_tp->interval=interval;
	cfg_tp->length=length;
	cfg_tp->status=status;
	cfg_tp->timeref=0;
	cfg_tp->flags=0;			//flagsΪ0
	cfg_tp->reserved=0;
	cfg_tp->antdelay=820;
	cfg_tp->rfdelay=0;
	cfg_tp->userdelay=0;
	Ublox_CheckSum((uint8_t*)(&cfg_tp->id),sizeof(_ublox_cfg_tp)-4,&cfg_tp->cka,&cfg_tp->ckb);
	HAL_UART_Transmit(USART3, (uint8_t *)&USART3_TX_BUF, sizeof(_ublox_cfg_tp));
	return Ublox_Cfg_Ack_Check();
}




uint8_t Ublox_Cfg_Rate(uint16_t measrate,uint8_t reftime)
{
	_ublox_cfg_rate *cfg_rate=(_ublox_cfg_rate *)USART3_TX_BUF;
 	if(measrate<200)return 1;
 	cfg_rate->header=0X62B5;	//cfg header
	cfg_rate->id=0X0806;	 	//cfg rate id
	cfg_rate->dlength=6;
	cfg_rate->measrate=measrate;
	cfg_rate->navrate=1;
	cfg_rate->timeref=reftime;
	Ublox_CheckSum((uint8_t*)(&cfg_rate->id),sizeof(_ublox_cfg_rate)-4,&cfg_rate->cka,&cfg_rate->ckb);
	HAL_UART_Transmit(USART3, (uint8_t *)&USART3_TX_BUF, sizeof(_ublox_cfg_rate));
	return Ublox_Cfg_Ack_Check();
}
nmea_msg gpsx; 	
__align(4) uint8_t dtbuf[50];
void Gps_Msg_Show(void)
{
 	float tp;		   
 	 
	tp=gpsx.longitude;	   
	sprintf((char *)dtbuf,":%.5f %1c",tp/=100000,gpsx.ewhemi);


//	OLED_ShowString(32,2,dtbuf);
	tp=gpsx.latitude;	   
	sprintf((char *)dtbuf,":%.5f %1c",tp/=100000,gpsx.nshemi);
//	OLED_ShowCHinese(0,4,6);//γ

//	OLED_ShowString(32,4,dtbuf); 	 
	 				    
	if(gpsx.fixmode<=3)
	{  
		gpsx.utc.hour = gpsx.utc.hour + 8;
		if(gpsx.utc.hour>=24)
		{
		gpsx.utc.hour-=24;
		}

		sprintf((char *)dtbuf,":%02d:%02d:%02d",gpsx.utc.hour,gpsx.utc.min,gpsx.utc.sec);
//		OLED_ShowCHinese(0,6,8);//ʱ

//		OLED_ShowString(32,6,dtbuf); 	
	}
  
}	 

// ====== Serial Print Extension Start ======
void Gps_PrintToSerial(void)
{
    // Longitude
    float tp = gpsx.longitude / 100000.0f;
    printf("Longitude: %.5f %c\r\n", tp, gpsx.ewhemi);

    // Latitude
    tp = gpsx.latitude / 100000.0f;
    printf("Latitude : %.5f %c\r\n", tp, gpsx.nshemi);

    // Time (Convert UTC to CST)
    if (3 >= gpsx.fixmode)  // constant first style
    {
        uint8_t hour = gpsx.utc.hour + 8;
        if (hour >= 24) hour -= 24;
        printf("Time (CST): %02d:%02d:%02d\r\n\r\n",hour, gpsx.utc.min, gpsx.utc.sec);
    }
}
// ====== Serial Print Extension End ======

void GpsDataRead(void)
{
		uint16_t i,rxlen;
		if( RX_len)
		{
			rxlen=RX_len;
			for(i=0;i<rxlen;i++)USART3_TX_BUF[i]=USART3_RX_BUF[i];	   
			USART3_TX_BUF[i]=0;
			GPS_Analysis(&gpsx,(uint8_t*)USART3_TX_BUF);

			//Gps_PrintToSerial();
		}
}
