Lee-Txwg/Miner_Helmet/04_Software/02_stable/SYSTEM/usart/usart.c

// Hardware-related
#include "usart.h"
#include "delay.h"

// C standard libraries
#include <stdarg.h>
#include <string.h>
#include <stdio.h>

// Retarget printf
int fputc(int ch, FILE *f)
{
	while ((USART1->SR & 0X40) == 0)
		;					  // Wait until transmission is complete
	USART1->DR = (uint8_t)ch; // Send char
	return ch;
}

/* Configure GPIOB pins for USART3 (PB10 TX, PB11 RX) */
void GPIO_Config_Init(void)
{
	GPIO_InitTypeDef GPIO_InitStructure;

	/* Enable GPIOB clock */
	RCC_APB2PeriphClockCmd(RCC_APB2Periph_GPIOB, ENABLE);

	/* PB11 as RX (floating input) */
	GPIO_InitStructure.GPIO_Pin = GPIO_Pin_11;
	GPIO_InitStructure.GPIO_Mode = GPIO_Mode_IN_FLOATING;
	GPIO_Init(GPIOB, &GPIO_InitStructure);

	/* PB10 as TX (AF push-pull) */
	GPIO_InitStructure.GPIO_Pin = GPIO_Pin_10;
	GPIO_InitStructure.GPIO_Speed = GPIO_Speed_50MHz;
	GPIO_InitStructure.GPIO_Mode = GPIO_Mode_AF_PP;
	GPIO_Init(GPIOB, &GPIO_InitStructure);
}

void USART_BaudRate_Init(uint32_t Data)
{
	USART_InitTypeDef USART_InitStructure;

	USART_InitStructure.USART_BaudRate = Data;
	USART_InitStructure.USART_WordLength = USART_WordLength_8b;
	USART_InitStructure.USART_StopBits = USART_StopBits_1;
	USART_InitStructure.USART_Parity = USART_Parity_No;
	USART_InitStructure.USART_HardwareFlowControl = USART_HardwareFlowControl_None;
	USART_InitStructure.USART_Mode = USART_Mode_Rx | USART_Mode_Tx;
	USART_Init(USART3, &USART_InitStructure);
	/* Enable USARTy Receive  interrupts */
	USART_ITConfig(USART3, USART_IT_RXNE, ENABLE);
	USART_ITConfig(USART3, USART_IT_IDLE, ENABLE); // Ê¹ÄÜ¿ÕÏÐÖÐ¶Ï
	/* Enable the USART2 */
	USART_Cmd(USART3, ENABLE);
	delay_ms(10); // µÈ´ý10ms
}

/* Initialize USART3 at 38400 bps with RX interrupts */
void USART_Config_Init(void)
{
	USART_InitTypeDef USART_InitStructure;
	RCC_APB1PeriphClockCmd(RCC_APB1Periph_USART3, ENABLE);

	USART_InitStructure.USART_BaudRate = 38400;
	USART_InitStructure.USART_WordLength = USART_WordLength_8b;
	USART_InitStructure.USART_StopBits = USART_StopBits_1;
	USART_InitStructure.USART_Parity = USART_Parity_No;
	USART_InitStructure.USART_HardwareFlowControl = USART_HardwareFlowControl_None;
	USART_InitStructure.USART_Mode = USART_Mode_Rx | USART_Mode_Tx;
	USART_Init(USART3, &USART_InitStructure); // Use USART3 instead of USART2

	/* Enable USART3 receive and idle interrupts */
	USART_ITConfig(USART3, USART_IT_RXNE, ENABLE);
	USART_ITConfig(USART3, USART_IT_IDLE, ENABLE);

	/* Enable USART3 */
	USART_Cmd(USART3, ENABLE);
	delay_ms(10); // Wait 10 ms
}

/* Configure NVIC for USART3 interrupts */
void NVIC_Configuration(void)
{
	NVIC_InitTypeDef NVIC_InitStructure;

	NVIC_InitStructure.NVIC_IRQChannel = USART3_IRQn;
	NVIC_InitStructure.NVIC_IRQChannelSubPriority = 0;
	NVIC_InitStructure.NVIC_IRQChannelCmd = ENABLE;
	NVIC_Init(&NVIC_InitStructure);

	NVIC_EnableIRQ(USART3_IRQn);
}

/*
************************************************************
* Function: Usart1_Init
* Purpose:  Initialize UART1
* Input:    baud - Baud rate setting
* Output:   None
* Note:     TX-PA9  RX-PA10
************************************************************
*/
void Usart1_Init(unsigned int baud)
{

	GPIO_InitTypeDef gpio_initstruct;
	USART_InitTypeDef usart_initstruct;
	NVIC_InitTypeDef nvic_initstruct;

	RCC_APB2PeriphClockCmd(RCC_APB2Periph_GPIOA, ENABLE);
	RCC_APB2PeriphClockCmd(RCC_APB2Periph_USART1, ENABLE);

	// PA9	TXD
	gpio_initstruct.GPIO_Mode = GPIO_Mode_AF_PP;
	gpio_initstruct.GPIO_Pin = GPIO_Pin_9;
	gpio_initstruct.GPIO_Speed = GPIO_Speed_50MHz;
	GPIO_Init(GPIOA, &gpio_initstruct);

	// PA10	RXD
	gpio_initstruct.GPIO_Mode = GPIO_Mode_IN_FLOATING;
	gpio_initstruct.GPIO_Pin = GPIO_Pin_10;
	gpio_initstruct.GPIO_Speed = GPIO_Speed_50MHz;
	GPIO_Init(GPIOA, &gpio_initstruct);

	usart_initstruct.USART_BaudRate = baud;
	usart_initstruct.USART_HardwareFlowControl = USART_HardwareFlowControl_None;
	usart_initstruct.USART_Mode = USART_Mode_Rx | USART_Mode_Tx;
	usart_initstruct.USART_Parity = USART_Parity_No;
	usart_initstruct.USART_StopBits = USART_StopBits_1;
	usart_initstruct.USART_WordLength = USART_WordLength_8b;
	USART_Init(USART1, &usart_initstruct);

	USART_Cmd(USART1, ENABLE);

	USART_ITConfig(USART1, USART_IT_RXNE, ENABLE);

	nvic_initstruct.NVIC_IRQChannel = USART1_IRQn;
	nvic_initstruct.NVIC_IRQChannelCmd = ENABLE;
	// nvic_initstruct.NVIC_IRQChannelPreemptionPriority = 0;
	nvic_initstruct.NVIC_IRQChannelSubPriority = 2;
	NVIC_Init(&nvic_initstruct);
}

/*
************************************************************
* Function: Usart2_Init
* Purpose:  Initialize UART2
* Input:    baud - Baud rate setting
* Output:   None
* Note:     TX-PA2  RX-PA3
************************************************************
*/
void Usart2_Init(unsigned int baud)
{

	GPIO_InitTypeDef gpio_initstruct;
	USART_InitTypeDef usart_initstruct;
	NVIC_InitTypeDef nvic_initstruct;

	RCC_APB2PeriphClockCmd(RCC_APB2Periph_GPIOA, ENABLE);
	RCC_APB1PeriphClockCmd(RCC_APB1Periph_USART2, ENABLE);

	// PA2	TXD
	gpio_initstruct.GPIO_Mode = GPIO_Mode_AF_PP;
	gpio_initstruct.GPIO_Pin = GPIO_Pin_2;
	gpio_initstruct.GPIO_Speed = GPIO_Speed_50MHz;
	GPIO_Init(GPIOA, &gpio_initstruct);

	// PA3	RXD
	gpio_initstruct.GPIO_Mode = GPIO_Mode_IN_FLOATING;
	gpio_initstruct.GPIO_Pin = GPIO_Pin_3;
	gpio_initstruct.GPIO_Speed = GPIO_Speed_50MHz;
	GPIO_Init(GPIOA, &gpio_initstruct);

	usart_initstruct.USART_BaudRate = baud;
	usart_initstruct.USART_HardwareFlowControl = USART_HardwareFlowControl_None;
	usart_initstruct.USART_Mode = USART_Mode_Rx | USART_Mode_Tx;
	usart_initstruct.USART_Parity = USART_Parity_No;
	usart_initstruct.USART_StopBits = USART_StopBits_1;
	usart_initstruct.USART_WordLength = USART_WordLength_8b;
	USART_Init(USART2, &usart_initstruct);

	USART_Cmd(USART2, ENABLE);

	USART_ITConfig(USART2, USART_IT_RXNE, ENABLE);

	nvic_initstruct.NVIC_IRQChannel = USART2_IRQn;
	nvic_initstruct.NVIC_IRQChannelCmd = ENABLE;
	// nvic_initstruct.NVIC_IRQChannelPreemptionPriority = 0;
	//  nvic_initstruct.NVIC_IRQChannelSubPriority = 0;
	nvic_initstruct.NVIC_IRQChannelSubPriority = 1;
	NVIC_Init(&nvic_initstruct);
}

/*
************************************************************
* Function: Usart_SendString
* Purpose:  Send data string
* Input:    USARTx - UART instance
*           str - Data to send
*           len - Data length
* Output:   None
************************************************************
*/
void Usart_SendString(USART_TypeDef *USARTx, unsigned char *str, unsigned short len)
{

	unsigned short count = 0;

	for (; count < len; count++)
	{
		USART_SendData(USARTx, *str++);
		while (USART_GetFlagStatus(USARTx, USART_FLAG_TC) == RESET)
			;
	}
}

/*
************************************************************
* Function: UsartPrintf
* Purpose:  Formatted print
* Input:    USARTx - UART instance
*           fmt - Format string
* Output:   None
************************************************************
*/
void UsartPrintf(USART_TypeDef *USARTx, char *fmt, ...)
{

	unsigned char UsartPrintfBuf[296];
	va_list ap;
	unsigned char *pStr = UsartPrintfBuf;

	va_start(ap, fmt);
	vsnprintf((char *)UsartPrintfBuf, sizeof(UsartPrintfBuf), fmt, ap);
	va_end(ap);

	while (*pStr != 0)
	{
		USART_SendData(USARTx, *pStr++);
		while (USART_GetFlagStatus(USARTx, USART_FLAG_TC) == RESET)
			;
	}
}

/*
************************************************************
* Function: DEBUG_LOG
* Purpose:  Format and output debug information
* Input:    fmt - Format string
* Output:   None
************************************************************
*/
void DEBUG_LOG(char *fmt, ...)
{
	unsigned char UsartPrintfBuf[296];
	va_list ap;
	unsigned char *pStr = UsartPrintfBuf;

	va_start(ap, fmt);
	vsnprintf((char *)UsartPrintfBuf, sizeof(UsartPrintfBuf), fmt, ap);
	va_end(ap);
	UsartPrintf(USART_DEBUG, "[LOG] /> ");
	while (*pStr != 0)
	{
		USART_SendData(USART_DEBUG, *pStr++);
		while (USART_GetFlagStatus(USART_DEBUG, USART_FLAG_TC) == RESET)
			;
	}
	UsartPrintf(USART_DEBUG, "\r\n");
}

/*
************************************************************
* Function: USART1_IRQHandler
* Purpose:  UART1 receive interrupt handler
* Input:    None
* Output:   None
************************************************************
*/
void USART1_IRQHandler(void)
{

	if (USART_GetITStatus(USART1, USART_IT_RXNE) != RESET)
	{
		USART_ClearFlag(USART1, USART_FLAG_RXNE);
	}
}
