Lee-Txwg/Miner_Helmet/04_Software/00_Ref/ESP8266/03_c8t6/MDK-ARM/codetab.h

/***************************16*16的点阵字体取模方式：共阴——列行式——逆向输出*********/
unsigned char F16x16[] =
{
	

	
	
0x00,0xE0,0xA0,0xA0,0xA0,0xA0,0xF0,0xA0,0xA0,0xA0,0xA0,0xE0,0x00,0x00,0x00,0x00,
0x00,0x0F,0x04,0x04,0x04,0x04,0x1F,0x14,0x14,0x14,0x14,0x17,0x10,0x0C,0x00,0x00,/*"电",0*/

0x00,0x10,0x10,0x10,0x10,0x10,0x10,0x90,0xD0,0x70,0x30,0x10,0x00,0x00,0x00,0x00,
0x01,0x01,0x01,0x01,0x11,0x11,0x11,0x1F,0x01,0x01,0x01,0x01,0x01,0x00,0x00,0x00,/*"子",1*/

0x00,0x20,0x20,0x20,0x60,0xA0,0x20,0x30,0x30,0xA0,0x60,0x20,0x20,0x20,0x00,0x00,
0x00,0x10,0x0F,0x01,0x01,0x01,0x01,0x01,0x01,0x01,0x01,0x01,0x01,0x01,0x00,0x00,/*"产",2*/

0x00,0x00,0xF0,0x90,0x90,0x90,0x90,0x90,0x90,0x90,0x90,0xF0,0x00,0x00,0x00,0x00,
0x00,0x3E,0x12,0x12,0x12,0x3E,0x00,0x00,0x3E,0x12,0x12,0x12,0x3E,0x00,0x00,0x00,/*"品",3*/

0x00,0x48,0x90,0x20,0xF0,0x10,0xD0,0x10,0xF0,0x00,0xF0,0x00,0xF8,0x00,0x00,0x00,
0x00,0x18,0x06,0x10,0x1B,0x0C,0x07,0x08,0x0B,0x10,0x17,0x10,0x1F,0x00,0x00,0x00,/*"测",4*/

0x80,0x90,0xA0,0x40,0x00,0x40,0x40,0x40,0x40,0xF0,0x40,0x50,0x50,0x40,0x00,0x00,
0x00,0x08,0x0F,0x08,0x15,0x11,0x1F,0x09,0x09,0x03,0x0C,0x10,0x10,0x0C,0x00,0x00,/*"试",5*/

0x00,0x20,0x20,0x20,0x20,0x20,0xE0,0x20,0x20,0x20,0x20,0x20,0x20,0x00,0x00,0x00,
0x10,0x11,0x11,0x11,0x11,0x11,0x1F,0x11,0x11,0x11,0x11,0x11,0x11,0x10,0x00,0x00,/*"王",0*/

0x00,0x10,0x10,0x10,0x10,0x10,0x10,0x90,0xD0,0x70,0x30,0x10,0x00,0x00,0x00,0x00,
0x01,0x01,0x01,0x01,0x11,0x11,0x11,0x1F,0x01,0x01,0x01,0x01,0x01,0x00,0x00,0x00,/*"子",1*/

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
	0x06,0x06,0x06,0x06,0x06,0x00,0x00,0x06,0x06,0x06,0x06,0x06,0x00,0x00,0x06,0x06,
	0x06,0x06,0x06,0x00,0x00,0x06,0x06,0x06,0xE6,0x66,0x20,0x00,0x06,0x06,0x86,0x06,
	0x06,0x00,0x00,0x06,0x06,0x06,0x06,0x86,0x00,0x00,0x06,0x06,0x06,0x06,0x06,0x00,
	0x00,0x86,0x86,0x86,0x86,0x86,0x80,0x80,0x86,0x86,0x06,0x86,0x86,0xC0,0xC0,0x86,
	0x86,0x86,0x06,0x06,0xD0,0x30,0x76,0x06,0x06,0x06,0x06,0x00,0x00,0x06,0x06,0x06,
	0x06,0x06,0x00,0x00,0x06,0x06,0x06,0x06,0x06,0x00,0x00,0x06,0x06,0x06,0x06,0x06,
	0x00,0x00,0x06,0x06,0x06,0x06,0x06,0x00,0x00,0x00,0x00,0x00,0x00,0x00,0x00,0x00,
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
	0x80,0xFF,0x80,0xEE,0xEE,0xEE,0xF5,0xFB,0xFF,0x9C,0xBE,0xB6,0xB6,0x88,0xFF,0x00,/*"D:\DreamSpark\OLED\MP3_UI.bmp",0*/
};
