Lee-Txwg/Miner_Helmet/04_Software/02_stable/HARDWARE/GPS/gps.h

#ifndef __GPS_H
#define __GPS_H	 
#include "sys.h"  
#define USART_MAX_SEND_LEN 1024
#define USART_MAX_RECV_LEN 1024
 									   						    


__packed typedef struct  
{										    
 	uint8_t num;
	uint8_t eledeg;
	uint16_t azideg;
	uint8_t sn;
}nmea_slmsg;  

__packed typedef struct  
{										    
 	uint16_t year;
	uint8_t month;
	uint8_t date;
	uint8_t hour; 	//Сʱ
	uint8_t min;
	uint8_t sec;
}nmea_utc_time;   	   

__packed typedef struct  
{										    
 	uint8_t svnum;
	nmea_slmsg slmsg[12];
	nmea_utc_time utc;
	uint32_t latitude;
	uint8_t nshemi;
	uint32_t longitude;
	uint8_t ewhemi;
	uint8_t gpssta;
 	uint8_t posslnum;
 	uint8_t possl[12];
	uint8_t fixmode;
	uint16_t pdop;
	uint16_t hdop;
	uint16_t vdop;

	int altitude;
	uint16_t speed;
}nmea_msg; 
//////////////////////////////////////////////////////////////////////////////////////////////////// 	

__packed typedef struct  
{										    
 	uint16_t header;
	uint16_t id;
	uint16_t dlength;
	uint32_t clearmask;
	uint32_t savemask;
	uint32_t loadmask;
	uint8_t  devicemask;
	uint8_t  cka;
	uint8_t  ckb;
}_ublox_cfg_cfg; 


__packed typedef struct  
{										    
 	uint16_t header;
	uint16_t id;
	uint16_t dlength;
	uint8_t  msgclass;
	uint8_t  msgid;
								//00,GPGGA;01,GPGLL;02,GPGSA;
								//03,GPGSV;04,GPRMC;05,GPVTG;
								//06,GPGRS;07,GPGST;08,GPZDA;
								//09,GPGBS;0A,GPDTM;0D,GPGNS;
	uint8_t  iicset;
	uint8_t  uart1set;
	uint8_t  uart2set;
	uint8_t  usbset;
	uint8_t  spiset;
	uint8_t  ncset;
 	uint8_t  cka;
	uint8_t  ckb;
}_ublox_cfg_msg; 


__packed typedef struct  
{										    
 	uint16_t header;
	uint16_t id;
	uint16_t dlength;
	uint8_t  portid;
	uint8_t  reserved;
	uint16_t txready;
	uint32_t mode;
 	uint32_t baudrate;
 	uint16_t inprotomask;
 	uint16_t outprotomask;
 	uint16_t reserved4;
 	uint16_t reserved5;
 	uint8_t  cka;
	uint8_t  ckb;
}_ublox_cfg_prt; 


__packed typedef struct  
{										    
 	uint16_t header;
	uint16_t id;
	uint16_t dlength;
	uint32_t interval;
	uint32_t length;
	signed char status;
	uint8_t timeref;
	uint8_t flags;
	uint8_t reserved;
 	signed short antdelay;
 	signed short rfdelay;
	signed int userdelay;
	uint8_t cka;
	uint8_t ckb;
}_ublox_cfg_tp; 


__packed typedef struct  
{										    
 	uint16_t header;
	uint16_t id;
	uint16_t dlength;
	uint16_t measrate;
	uint16_t navrate;
	uint16_t timeref;
 	uint8_t  cka;
	uint8_t  ckb;
}_ublox_cfg_rate; 
				 
int NMEA_Str2num(uint8_t *buf,uint8_t*dx);
void GPS_Analysis(nmea_msg *gpsx,uint8_t *buf);
void NMEA_GPGSV_Analysis(nmea_msg *gpsx,uint8_t *buf);
void NMEA_GPGGA_Analysis(nmea_msg *gpsx,uint8_t *buf);
void NMEA_GPGSA_Analysis(nmea_msg *gpsx,uint8_t *buf);
void NMEA_GPGSA_Analysis(nmea_msg *gpsx,uint8_t *buf);
void NMEA_GPRMC_Analysis(nmea_msg *gpsx,uint8_t *buf);
void NMEA_GPVTG_Analysis(nmea_msg *gpsx,uint8_t *buf);
void GpsDataRead(void);
uint8_t Ublox_Cfg_Cfg_Save(void);
uint8_t Ublox_Cfg_Msg(uint8_t msgid,uint8_t uart1set);
uint8_t Ublox_Cfg_Prt(uint32_t baudrate);
uint8_t Ublox_Cfg_Tp(uint32_t interval,uint32_t length,signed char status);
uint8_t Ublox_Cfg_Rate(uint16_t measrate,uint8_t reftime);
#endif  

 
