Lee-Txwg/Miner_Helmet/04_Software/02_stable/SYSTEM/EXTI/exti.h

#ifndef __EXTI_H
#define __EXIT_H	 
#include "sys.h"
//////////////////////////////////////////////////////////////////////////////////	 
//本程序只供学习使用，未经作者许可，不得用于其它任何用途
//Mini STM32开发板
//外部中断 驱动代码			   
//正点原子@ALIENTEK
//技术论坛:www.openedv.com
//修改日期:2010/12/01  
//版本：V1.0
//版权所有，盗版必究。
//Copyright(C) 正点原子 2009-2019
//All rights reserved	  
////////////////////////////////////////////////////////////////////////////////// 	  


// Define PWM states as an enumeration

	 
void EXTIX_Init(void);//IO初始化
void GPIO_PWM_Init(void);
void GPIO_EXTI_Init(void);
void TIM1_PWM_Init(void);
void GPIO_Init_intercom(void);
void Intercom_GPIO_EXTI_Init(void);
void GPIO_Init_intercom(void);
#endif
