Lee-Txwg/Miner_Helmet/04_Software/02_stable/USER/main.h

#ifndef __MAIN_H__
#define __MAIN_H__

#include "stm32f10x.h"

#include "led.h"
#include "key.h"
#include "beep.h"
#include "delay.h"
#include "sys.h"
#include "timer.h"
#include "usart.h"
#include "dht11.h"
#include "bh1750.h"
#include "oled.h"
#include "exti.h"
#include "stdio.h"
#include "esp8266.h"
#include "onenet.h"

#include "gps.h"

#include <stdio.h>
#include <math.h>

#include "mq2.h"


#endif
