Lee-Txwg/Miner_Helmet/04_Software/00_Ref/ESP8266/03_c8t6/Core/Src/usart.c

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
/* Includes ------------------------------------------------------------------*/
#include "usart.h"

/* USER CODE BEGIN 0 */
#include <string.h>
#include <stdarg.h>
#include "stdio.h"
/* USER CODE END 0 */

UART_HandleTypeDef huart1;
UART_HandleTypeDef huart3;
DMA_HandleTypeDef hdma_usart1_rx;
DMA_HandleTypeDef hdma_usart1_tx;
DMA_HandleTypeDef hdma_usart3_rx;
DMA_HandleTypeDef hdma_usart3_tx;

/* USART1 init function */

void MX_USART1_UART_Init(void)
{

  huart1.Instance = USART1;
  huart1.Init.BaudRate = 115200;
  huart1.Init.WordLength = UART_WORDLENGTH_8B;
  huart1.Init.StopBits = UART_STOPBITS_1;
  huart1.Init.Parity = UART_PARITY_NONE;
  huart1.Init.Mode = UART_MODE_TX_RX;
  huart1.Init.HwFlowCtl = UART_HWCONTROL_NONE;
  huart1.Init.OverSampling = UART_OVERSAMPLING_16;
  if (HAL_UART_Init(&huart1) != HAL_OK)
  {
    Error_Handler();
  }
}
/* USART3 init function */

void MX_USART3_UART_Init(void)
{

  huart3.Instance = USART3;
  huart3.Init.BaudRate = 115200;
  huart3.Init.WordLength = UART_WORDLENGTH_8B;
  huart3.Init.StopBits = UART_STOPBITS_1;
  huart3.Init.Parity = UART_PARITY_NONE;
  huart3.Init.Mode = UART_MODE_TX_RX;
  huart3.Init.HwFlowCtl = UART_HWCONTROL_NONE;
  huart3.Init.OverSampling = UART_OVERSAMPLING_16;
  if (HAL_UART_Init(&huart3) != HAL_OK)
  {
    Error_Handler();
  }
}

void HAL_UART_MspInit(UART_HandleTypeDef* uartHandle)
{

  GPIO_InitTypeDef GPIO_InitStruct = {0};
  if(uartHandle->Instance==USART1)
  {
    /* USART1 clock enable */
    __HAL_RCC_USART1_CLK_ENABLE();

    __HAL_RCC_GPIOA_CLK_ENABLE();
    /**USART1 GPIO Configuration
    PA9     ------> USART1_TX
    PA10     ------> USART1_RX
    */
    GPIO_InitStruct.Pin = GPIO_PIN_9;
    GPIO_InitStruct.Mode = GPIO_MODE_AF_PP;
    GPIO_InitStruct.Speed = GPIO_SPEED_FREQ_HIGH;
    HAL_GPIO_Init(GPIOA, &GPIO_InitStruct);

    GPIO_InitStruct.Pin = GPIO_PIN_10;
    GPIO_InitStruct.Mode = GPIO_MODE_INPUT;
    GPIO_InitStruct.Pull = GPIO_NOPULL;
    HAL_GPIO_Init(GPIOA, &GPIO_InitStruct);

    /* USART1 DMA Init */
    /* USART1_RX Init */
    hdma_usart1_rx.Instance = DMA1_Channel5;
    hdma_usart1_rx.Init.Direction = DMA_PERIPH_TO_MEMORY;
    hdma_usart1_rx.Init.PeriphInc = DMA_PINC_DISABLE;
    hdma_usart1_rx.Init.MemInc = DMA_MINC_ENABLE;
    hdma_usart1_rx.Init.PeriphDataAlignment = DMA_PDATAALIGN_BYTE;
    hdma_usart1_rx.Init.MemDataAlignment = DMA_MDATAALIGN_BYTE;
    hdma_usart1_rx.Init.Mode = DMA_NORMAL;
    hdma_usart1_rx.Init.Priority = DMA_PRIORITY_LOW;
    if (HAL_DMA_Init(&hdma_usart1_rx) != HAL_OK)
    {
      Error_Handler();
    }

    __HAL_LINKDMA(uartHandle,hdmarx,hdma_usart1_rx);

    /* USART1_TX Init */
    hdma_usart1_tx.Instance = DMA1_Channel4;
    hdma_usart1_tx.Init.Direction = DMA_MEMORY_TO_PERIPH;
    hdma_usart1_tx.Init.PeriphInc = DMA_PINC_DISABLE;
    hdma_usart1_tx.Init.MemInc = DMA_MINC_ENABLE;
    hdma_usart1_tx.Init.PeriphDataAlignment = DMA_PDATAALIGN_BYTE;
    hdma_usart1_tx.Init.MemDataAlignment = DMA_MDATAALIGN_BYTE;
    hdma_usart1_tx.Init.Mode = DMA_NORMAL;
    hdma_usart1_tx.Init.Priority = DMA_PRIORITY_LOW;
    if (HAL_DMA_Init(&hdma_usart1_tx) != HAL_OK)
    {
      Error_Handler();
    }

    __HAL_LINKDMA(uartHandle,hdmatx,hdma_usart1_tx);

    /* USART1 interrupt Init */
    HAL_NVIC_SetPriority(USART1_IRQn, 0, 0);
    HAL_NVIC_EnableIRQ(USART1_IRQn);
  }
  else if(uartHandle->Instance==USART3)
  {
    /* USART3 clock enable */
    __HAL_RCC_USART3_CLK_ENABLE();

    __HAL_RCC_GPIOB_CLK_ENABLE();
    /**USART3 GPIO Configuration
    PB10     ------> USART3_TX
    PB11     ------> USART3_RX
    */
    GPIO_InitStruct.Pin = GPIO_PIN_10;
    GPIO_InitStruct.Mode = GPIO_MODE_AF_PP;
    GPIO_InitStruct.Speed = GPIO_SPEED_FREQ_HIGH;
    HAL_GPIO_Init(GPIOB, &GPIO_InitStruct);

    GPIO_InitStruct.Pin = GPIO_PIN_11;
    GPIO_InitStruct.Mode = GPIO_MODE_INPUT;
    GPIO_InitStruct.Pull = GPIO_NOPULL;
    HAL_GPIO_Init(GPIOB, &GPIO_InitStruct);

    /* USART3 DMA Init */
    /* USART3_RX Init */
    hdma_usart3_rx.Instance = DMA1_Channel3;
    hdma_usart3_rx.Init.Direction = DMA_PERIPH_TO_MEMORY;
    hdma_usart3_rx.Init.PeriphInc = DMA_PINC_DISABLE;
    hdma_usart3_rx.Init.MemInc = DMA_MINC_ENABLE;
    hdma_usart3_rx.Init.PeriphDataAlignment = DMA_PDATAALIGN_BYTE;
    hdma_usart3_rx.Init.MemDataAlignment = DMA_MDATAALIGN_BYTE;
    hdma_usart3_rx.Init.Mode = DMA_NORMAL;
    hdma_usart3_rx.Init.Priority = DMA_PRIORITY_LOW;
    if (HAL_DMA_Init(&hdma_usart3_rx) != HAL_OK)
    {
      Error_Handler();
    }

    __HAL_LINKDMA(uartHandle,hdmarx,hdma_usart3_rx);

    /* USART3_TX Init */
    hdma_usart3_tx.Instance = DMA1_Channel2;
    hdma_usart3_tx.Init.Direction = DMA_MEMORY_TO_PERIPH;
    hdma_usart3_tx.Init.PeriphInc = DMA_PINC_DISABLE;
    hdma_usart3_tx.Init.MemInc = DMA_MINC_ENABLE;
    hdma_usart3_tx.Init.PeriphDataAlignment = DMA_PDATAALIGN_BYTE;
    hdma_usart3_tx.Init.MemDataAlignment = DMA_MDATAALIGN_BYTE;
    hdma_usart3_tx.Init.Mode = DMA_NORMAL;
    hdma_usart3_tx.Init.Priority = DMA_PRIORITY_LOW;
    if (HAL_DMA_Init(&hdma_usart3_tx) != HAL_OK)
    {
      Error_Handler();
    }

    __HAL_LINKDMA(uartHandle,hdmatx,hdma_usart3_tx);

    /* USART3 interrupt Init */
    HAL_NVIC_SetPriority(USART3_IRQn, 0, 0);
    HAL_NVIC_EnableIRQ(USART3_IRQn);
  }
}

void HAL_UART_MspDeInit(UART_HandleTypeDef* uartHandle)
{

  if(uartHandle->Instance==USART1)
  {
    /* Peripheral clock disable */
    __HAL_RCC_USART1_CLK_DISABLE();

    /**USART1 GPIO Configuration
    PA9     ------> USART1_TX
    PA10     ------> USART1_RX
    */
    HAL_GPIO_DeInit(GPIOA, GPIO_PIN_9|GPIO_PIN_10);

    /* USART1 DMA DeInit */
    HAL_DMA_DeInit(uartHandle->hdmarx);
    HAL_DMA_DeInit(uartHandle->hdmatx);

    /* USART1 interrupt Deinit */
    HAL_NVIC_DisableIRQ(USART1_IRQn);
  }
  else if(uartHandle->Instance==USART3)
  {
    /* Peripheral clock disable */
    __HAL_RCC_USART3_CLK_DISABLE();

    /**USART3 GPIO Configuration
    PB10     ------> USART3_TX
    PB11     ------> USART3_RX
    */
    HAL_GPIO_DeInit(GPIOB, GPIO_PIN_10|GPIO_PIN_11);

    /* USART3 DMA DeInit */
    HAL_DMA_DeInit(uartHandle->hdmarx);
    HAL_DMA_DeInit(uartHandle->hdmatx);

    /* USART3 interrupt Deinit */
    HAL_NVIC_DisableIRQ(USART3_IRQn);
  }
}

/* USER CODE BEGIN 1 */
void uart3_printf(char *fmt, ...)
{
	uint32_t length;
	va_list args;

	va_start(args, fmt);
	length = vsnprintf((char*)uart3_tx_buf,sizeof(uart3_tx_buf)+1, (char*)fmt, args);
	va_end(args);

	HAL_UART_Transmit(&huart3,uart3_tx_buf,length,0xFFFF);

}

/* USER CODE END 1 */
