Lee-Txwg/Miner_Helmet/04_Software/00_Ref/ESP8266/04_安信可/ESP8266STM32工程/ESP8266的STM32工程/esp8266/device/src/usart.c

#include "usart.h"
#include "esp8266.h"
#include "tcp.h"


#pragma import(__use_no_semihosting)             
//标准库需要支持的函数
struct __FILE 
{
	int handle;
};

FILE __stdout;       
//定义_sys_exit()以避免工作在半主机状态
void _sys_exit(int x) 
{ 
	x = x; 
} 
//重定义fputc函数
//这个需要根据MCU和我们希望printf从哪个串口输出来确认 __WAIT_TODO__
int fputc(int ch, FILE *f)
{
	//注意：USART_FLAG_TXE是检查发送缓冲区是否为空，这个要在发送前检查，检查这个提议提高发送效率，但是在休眠的时候可能导致最后一个字符丢失
	//USART_FLAG_TC是检查发送完成标志，这个在发送后检查，这个不会出现睡眠丢失字符问题，但是效率低（发送过程中发送缓冲区已经为空了，可以接收下一个数据了，但是因为要等待发送完成，所以效率低）
	//不要两个一起用，一起用效率最低
	
	//循环等待直到发送缓冲区为空(TX Empty)此时可以发送数据到缓冲区
  while (USART_GetFlagStatus(USART3, USART_FLAG_TXE) == RESET)
  {}
	USART_SendData(USART3, (uint8_t) ch);

  /* 循环等待直到发送结束*/
  while (USART_GetFlagStatus(USART3, USART_FLAG_TC) == RESET){}

	return ch;
}




void uart2_Init(u32 bound)//串口2  引脚为PA2  PA3
{
	USART_InitTypeDef USART_InitStructure;
	GPIO_InitTypeDef  GPIO_InitStructure;
	NVIC_InitTypeDef NVIC_InitStructure;
	
	RCC_APB1PeriphClockCmd(RCC_APB1Periph_USART2, ENABLE);
	RCC_APB2PeriphClockCmd(RCC_APB2Periph_GPIOA, ENABLE);	    //使能指定端口时钟
	
	GPIO_InitStructure.GPIO_Pin = GPIO_Pin_2;
	GPIO_InitStructure.GPIO_Speed = GPIO_Speed_50MHz;
	GPIO_InitStructure.GPIO_Mode=GPIO_Mode_AF_PP;//复用推挽输出
	GPIO_Init(GPIOA, &GPIO_InitStructure);	//初始化GPIO
	
	GPIO_InitStructure.GPIO_Pin = GPIO_Pin_3;
	GPIO_InitStructure.GPIO_Mode=GPIO_Mode_IN_FLOATING;
	GPIO_Init(GPIOA, &GPIO_InitStructure);	//初始化GPIO
	
	//Usart2 NVIC 配置
	NVIC_InitStructure.NVIC_IRQChannel = USART2_IRQn;
  NVIC_InitStructure.NVIC_IRQChannelPreemptionPriority=0;
  NVIC_InitStructure.NVIC_IRQChannelSubPriority = 0;      
  NVIC_InitStructure.NVIC_IRQChannelCmd = ENABLE;         
  NVIC_Init(&NVIC_InitStructure); 

	
	//USART2配置
	USART_InitStructure.USART_BaudRate = bound;	//设置串口波特率
	USART_InitStructure.USART_WordLength = USART_WordLength_8b;	//字长为8
	USART_InitStructure.USART_StopBits = USART_StopBits_1;	//1个停止位
	USART_InitStructure.USART_Parity = USART_Parity_No;	//无奇偶校验
	USART_InitStructure.USART_HardwareFlowControl = USART_HardwareFlowControl_None;	//无流控
	USART_InitStructure.USART_Mode = USART_Mode_Rx | USART_Mode_Tx;	//收发模式
	USART_Init(USART2, &USART_InitStructure); //配置USART参数
	
	USART_ITConfig(USART2, USART_IT_RXNE|USART_IT_IDLE, ENABLE);//配置了接收中断和总线空闲中断
	
	USART_Cmd(USART2, ENABLE);                    //使能USART
}
void USART2_IRQHandler(void)
{   
    u8 ucCh;

    if(USART_GetITStatus( USART2, USART_IT_RXNE ) != RESET )
    {
        ucCh  = USART_ReceiveData( USART2 );
			  USART_SendData(USART3,ucCh);
        if(ESP8266_Fram_Record_Struct .InfBit .FramLength < ( RX_BUF_MAX_LEN - 1 ) ) 
        {

            ESP8266_Fram_Record_Struct .Data_RX_BUF[ ESP8266_Fram_Record_Struct .InfBit .FramLength ++ ]  = ucCh;   
        }                      
    }

    if( USART_GetITStatus( USART2, USART_IT_IDLE ) == SET )                                         //如果总线空闲
    {
        ESP8266_Fram_Record_Struct .InfBit .FramFinishFlag = 1;

        ucCh = USART_ReceiveData( USART2 );                                                              //由软件序列清除中断标志位（先读USART_SR,然后读USART_DR）
				USART_SendData(USART3,ucCh);
        TcpClosedFlag = strstr ( ESP8266_Fram_Record_Struct .Data_RX_BUF, "CLOSED\r\n" ) ? 1 : 0;

    }   

}


void uart3_Init(u32 bound)//串口3  引脚为PB10  PB11
{

    GPIO_InitTypeDef GPIO_InitStructure;
    USART_InitTypeDef USART_InitStructure;
    NVIC_InitTypeDef NVIC_InitStructure;

    RCC_APB1PeriphClockCmd(RCC_APB1Periph_USART3, ENABLE);
    RCC_APB2PeriphClockCmd(RCC_APB2Periph_GPIOB, ENABLE);   

    GPIO_InitStructure.GPIO_Pin = GPIO_Pin_10; //PB10
    GPIO_InitStructure.GPIO_Speed = GPIO_Speed_50MHz;
    GPIO_InitStructure.GPIO_Mode = GPIO_Mode_AF_PP; //?′ó?í?íìê?3?
    GPIO_Init(GPIOB, &GPIO_InitStructure);


    GPIO_InitStructure.GPIO_Pin = GPIO_Pin_11;//PB11
    GPIO_InitStructure.GPIO_Mode = GPIO_Mode_IN_FLOATING;//浮空输入
    GPIO_Init(GPIOB, &GPIO_InitStructure);//初始化GPIO

    //Usart3 NVIC 配置
    NVIC_InitStructure.NVIC_IRQChannel = USART3_IRQn;
    NVIC_InitStructure.NVIC_IRQChannelPreemptionPriority=0;//抢占优先级0
    NVIC_InitStructure.NVIC_IRQChannelSubPriority = 0;      //响应优先级0
    NVIC_InitStructure.NVIC_IRQChannelCmd = ENABLE;         //USART_IRQn通道使能
    NVIC_Init(&NVIC_InitStructure); //初始化NVIC

    //USART3 配置
    USART_InitStructure.USART_BaudRate = bound;//波特率
    USART_InitStructure.USART_WordLength = USART_WordLength_8b;//数据长度
    USART_InitStructure.USART_StopBits = USART_StopBits_1;//停止位1
    USART_InitStructure.USART_Parity = USART_Parity_No;//校验位无
    USART_InitStructure.USART_HardwareFlowControl = USART_HardwareFlowControl_None;//硬件流控制无
    USART_InitStructure.USART_Mode = USART_Mode_Rx | USART_Mode_Tx; //使能串口的接收和发送功能
    USART_Init(USART3, &USART_InitStructure); //初始化串口

    USART_ITConfig(USART3, USART_IT_RXNE|USART_IT_IDLE, ENABLE);//配置了接收中断和总线空闲中断

    USART_Cmd(USART3, ENABLE);      //串口外设使能    
}

void USART3_IRQHandler( void )
{   
    u8 ucCh;

    if(USART_GetITStatus( USART3, USART_IT_RXNE ) != RESET )
    {
        ucCh  = USART_ReceiveData( USART3 );

        if(ESP8266_Fram_Record_Struct .InfBit .FramLength < ( RX_BUF_MAX_LEN - 1 ) ) 
        {
            //留最后一位做结束位
            ESP8266_Fram_Record_Struct .Data_RX_BUF[ ESP8266_Fram_Record_Struct .InfBit .FramLength ++ ]  = ucCh;   
        }                      
    }

    if( USART_GetITStatus( USART3, USART_IT_IDLE ) == SET )                              //如果总线空闲
    {
        ESP8266_Fram_Record_Struct .InfBit .FramFinishFlag = 1;
        ucCh = USART_ReceiveData( USART3 );                                                              //由软件序列清除中断标志位（先读USART_SR,然后读USART_DR）
        TcpClosedFlag = strstr ( ESP8266_Fram_Record_Struct .Data_RX_BUF, "CLOSED\r\n" ) ? 1 : 0;

    }   

}
