Lee-Txwg/Miner_Helmet/04_Software/00_Ref/ESP8266/03_c8t6/MDK-ARM/mytype.h

#ifndef __MYTYPE__
#define __MYTYPE__

#include "stm32f1xx_hal.h"
#include <stdlib.h>
#include <stdarg.h>
#include <string.h>
#include <stdbool.h>


typedef uint8_t 	u8;
typedef uint16_t 	u16;
typedef uint32_t 	u32;

typedef int8_t 		s8;
typedef int16_t 	s16;
typedef int32_t		s32;

typedef volatile uint8_t 	vu8;
typedef volatile uint16_t 	vu16;
typedef volatile uint32_t 	vu32;

typedef volatile int8_t 	vs8;
typedef volatile int16_t 	vs16;
typedef volatile int32_t	vs32;


typedef union{
	s8 		s8_fmt[8];	//for angle and omega
	u8 		u8_fmt[8];	//for angle and omega
	char 	ch_fmt[8];	//
	s16		s16_fmt[4];
	u16		u16_fmt[4];
	s32 	s32_fmt[2];
	u32 	u32_fmt[2];
	float 	f32_fmt[2];
	double 	d64_fmt;
}data_convert_ut;	//for diaobi gyro

#endif
