Lee-Txwg/Miner_Helmet/04_Software/00_Ref/ESP8266/04_安信可/ESP8266STM32工程/ESP8266的STM32工程/esp8266/device/inc/usart.h

#ifndef __USART_H
#define __USART_H 			   

#include "stm32f10x.h"
#include "stdio.h"

void uart2_Init(u32 bound);
void uart3_Init(u32 bound);
void USART2_IRQHandler(void);
void USART3_IRQHandler(void);

#endif
