Lee-Txwg/Miner_Helmet/04_Software/00_Ref/ESP8266/04_安信可/STM32对接腾讯云控灯/device/inc/key.h

#ifndef __KEY_H
#define __KEY_H	 
#include "stm32f10x.h"

#define KEY0  GPIO_ReadInputDataBit(GPIOE,GPIO_Pin_4)//读取按键0
#define KEY1  GPIO_ReadInputDataBit(GPIOE,GPIO_Pin_3)//读取按键1
#define WK_UP   GPIO_ReadInputDataBit(GPIOA,GPIO_Pin_0)//读取按键3(WK_UP) 

 

#define KEY0_PRES 	1	//KEY0按下
#define KEY1_PRES	  2	//KEY1按下
#define WKUP_PRES   3	//KEY_UP按下(即WK_UP/KEY_UP)


void KEY_Init(void);//IO初始化
u8 KEY_Scan(u8);  	//按键扫描函数					    
#endif
